masaleiro/HacKeyboard/Pre-compiled/18f4550_usb_hid_keyboard.asm

; compiler: jal 2.4p (compiled Sep  3 2012)

; command line:  ./jalv2 18f4550_usb_hid_keyboard.jal -s ../lib/ -no-variable-reuse
                                list p=18f4550, r=dec
                                errorlevel -306 ; no page boundary warnings
                                errorlevel -302 ; no bank 0 warnings
                                errorlevel -202 ; no 'argument out of range' warnings

                             __config 0x00300000, 0x24
                             __config 0x00300001, 0x0e
                             __config 0x00300002, 0x39
                             __config 0x00300003, 0x1e
                             __config 0x00300004, 0x00
                             __config 0x00300005, 0x85
                             __config 0x00300006, 0xc0
                             __config 0x00300007, 0x00
                             __config 0x00300008, 0x0f
                             __config 0x00300009, 0xc0
                             __config 0x0030000a, 0x0f
                             __config 0x0030000b, 0xe0
                             __config 0x0030000c, 0x0f
                             __config 0x0030000d, 0x40
v_true                         EQU 1
v_false                        EQU 0
v_high                         EQU 1
v_low                          EQU 0
v_input                        EQU 1
v_output                       EQU 0
v__pic_accum                   EQU 0x0000  ; _pic_accum
v_uir                          EQU 0x0f68  ; uir
v_uir_sofif                    EQU 0x0f68  ; uir_sofif-->uir:6
v_uir_stallif                  EQU 0x0f68  ; uir_stallif-->uir:5
v_uir_idleif                   EQU 0x0f68  ; uir_idleif-->uir:4
v_uir_trnif                    EQU 0x0f68  ; uir_trnif-->uir:3
v_uir_uerrif                   EQU 0x0f68  ; uir_uerrif-->uir:1
v_uir_urstif                   EQU 0x0f68  ; uir_urstif-->uir:0
v_uie                          EQU 0x0f69  ; uie
v_ueir                         EQU 0x0f6a  ; ueir
v_ustat                        EQU 0x0f6c  ; ustat
v_ustat_dir                    EQU 0x0f6c  ; ustat_dir-->ustat:2
v_ucon                         EQU 0x0f6d  ; ucon
v_ucon_pktdis                  EQU 0x0f6d  ; ucon_pktdis-->ucon:4
v_ucon_usben                   EQU 0x0f6d  ; ucon_usben-->ucon:3
v_uaddr                        EQU 0x0f6e  ; uaddr
v_ucfg                         EQU 0x0f6f  ; ucfg
v_uep0                         EQU 0x0f70  ; uep0
v_uep1                         EQU 0x0f71  ; uep1
v_uep2                         EQU 0x0f72  ; uep2
v_uep3                         EQU 0x0f73  ; uep3
v_uep4                         EQU 0x0f74  ; uep4
v_uep5                         EQU 0x0f75  ; uep5
v_uep6                         EQU 0x0f76  ; uep6
v_uep7                         EQU 0x0f77  ; uep7
v_uep8                         EQU 0x0f78  ; uep8
v_uep9                         EQU 0x0f79  ; uep9
v_uep10                        EQU 0x0f7a  ; uep10
v_uep11                        EQU 0x0f7b  ; uep11
v_uep12                        EQU 0x0f7c  ; uep12
v_uep13                        EQU 0x0f7d  ; uep13
v_uep14                        EQU 0x0f7e  ; uep14
v_uep15                        EQU 0x0f7f  ; uep15
v_portb                        EQU 0x0f81  ; portb
v_portc                        EQU 0x0f82  ; portc
v_portd                        EQU 0x0f83  ; portd
v_porte                        EQU 0x0f84  ; porte
v_lata                         EQU 0x0f89  ; lata
v_latb                         EQU 0x0f8a  ; latb
v_pin_b1                       EQU 0x0f81  ; pin_b1-->portb:1
v_pin_b0                       EQU 0x0f81  ; pin_b0-->portb:0
v_latc                         EQU 0x0f8b  ; latc
v_pin_c2                       EQU 0x0f82  ; pin_c2-->portc:2
v_pin_c1                       EQU 0x0f82  ; pin_c1-->portc:1
v_pin_c0                       EQU 0x0f82  ; pin_c0-->portc:0
v_latd                         EQU 0x0f8c  ; latd
v_pin_d2                       EQU 0x0f83  ; pin_d2-->portd:2
v_pin_d0                       EQU 0x0f83  ; pin_d0-->portd:0
v_late                         EQU 0x0f8d  ; late
v_pin_e2                       EQU 0x0f84  ; pin_e2-->porte:2
v_pin_e1                       EQU 0x0f84  ; pin_e1-->porte:1
v_trisa                        EQU 0x0f92  ; trisa
v_trisa_trisa5                 EQU 0x0f92  ; trisa_trisa5-->trisa:5
v_trisa_trisa4                 EQU 0x0f92  ; trisa_trisa4-->trisa:4
v_trisa_trisa3                 EQU 0x0f92  ; trisa_trisa3-->trisa:3
v_trisa_trisa2                 EQU 0x0f92  ; trisa_trisa2-->trisa:2
v_trisa_trisa1                 EQU 0x0f92  ; trisa_trisa1-->trisa:1
v_trisa_trisa0                 EQU 0x0f92  ; trisa_trisa0-->trisa:0
v_trisb                        EQU 0x0f93  ; trisb
v_trisb_trisb7                 EQU 0x0f93  ; trisb_trisb7-->trisb:7
v_trisb_trisb6                 EQU 0x0f93  ; trisb_trisb6-->trisb:6
v_trisb_trisb5                 EQU 0x0f93  ; trisb_trisb5-->trisb:5
v_trisb_trisb4                 EQU 0x0f93  ; trisb_trisb4-->trisb:4
v_trisb_trisb3                 EQU 0x0f93  ; trisb_trisb3-->trisb:3
v_trisb_trisb2                 EQU 0x0f93  ; trisb_trisb2-->trisb:2
v_trisb_trisb1                 EQU 0x0f93  ; trisb_trisb1-->trisb:1
v_trisb_trisb0                 EQU 0x0f93  ; trisb_trisb0-->trisb:0
v_trisc                        EQU 0x0f94  ; trisc
v_trisc_trisc2                 EQU 0x0f94  ; trisc_trisc2-->trisc:2
v_trisc_trisc1                 EQU 0x0f94  ; trisc_trisc1-->trisc:1
v_trisc_trisc0                 EQU 0x0f94  ; trisc_trisc0-->trisc:0
v_trisd                        EQU 0x0f95  ; trisd
v_trisd_trisd7                 EQU 0x0f95  ; trisd_trisd7-->trisd:7
v_trisd_trisd6                 EQU 0x0f95  ; trisd_trisd6-->trisd:6
v_trisd_trisd5                 EQU 0x0f95  ; trisd_trisd5-->trisd:5
v_trisd_trisd4                 EQU 0x0f95  ; trisd_trisd4-->trisd:4
v_trisd_trisd2                 EQU 0x0f95  ; trisd_trisd2-->trisd:2
v_trisd_trisd0                 EQU 0x0f95  ; trisd_trisd0-->trisd:0
v_trise                        EQU 0x0f96  ; trise
v_trise_trise2                 EQU 0x0f96  ; trise_trise2-->trise:2
v_trise_trise1                 EQU 0x0f96  ; trise_trise1-->trise:1
v_trise_trise0                 EQU 0x0f96  ; trise_trise0-->trise:0
v_pie2                         EQU 0x0fa0  ; pie2
v_pie2_usbie                   EQU 0x0fa0  ; pie2_usbie-->pie2:5
v_pir2                         EQU 0x0fa1  ; pir2
v_pir2_usbif                   EQU 0x0fa1  ; pir2_usbif-->pir2:5
v_eecon1                       EQU 0x0fa6  ; eecon1
v_eecon1_eepgd                 EQU 0x0fa6  ; eecon1_eepgd-->eecon1:7
v_eecon1_cfgs                  EQU 0x0fa6  ; eecon1_cfgs-->eecon1:6
v_eecon1_wren                  EQU 0x0fa6  ; eecon1_wren-->eecon1:2
v_eecon1_wr                    EQU 0x0fa6  ; eecon1_wr-->eecon1:1
v_eecon1_rd                    EQU 0x0fa6  ; eecon1_rd-->eecon1:0
v_eecon2                       EQU 0x0fa7  ; eecon2
v_eedata                       EQU 0x0fa8  ; eedata
v_eeadr                        EQU 0x0fa9  ; eeadr
v_cmcon                        EQU 0x0fb4  ; cmcon
v_adcon2                       EQU 0x0fc0  ; adcon2
v_adcon1                       EQU 0x0fc1  ; adcon1
v_adcon0                       EQU 0x0fc2  ; adcon0
v__status                      EQU 0x0fd8  ; _status
v__z                           EQU 2
v__c                           EQU 0
v__banked                      EQU 1
v__access                      EQU 0
v_fsr1l                        EQU 0x0fe1  ; fsr1l
v_fsr1h                        EQU 0x0fe2  ; fsr1h
v_postinc1                     EQU 0x0fe6  ; postinc1
v__fsr0l                       EQU 0x0fe9  ; _fsr0l
v__fsr0h                       EQU 0x0fea  ; _fsr0h
v__ind                         EQU 0x0fef  ; _ind
v_intcon                       EQU 0x0ff2  ; intcon
v_intcon_gie                   EQU 0x0ff2  ; intcon_gie-->intcon:7
v__tablat                      EQU 0x0ff5  ; _tablat
v__tblptr                      EQU 0x0ff6  ; _tblptr
v_usb_hid_endpoint             EQU 1
v_usb_in_delivery_buffer_loc   EQU 1144
v_usb_delivery_buffer          EQU 0x0478  ; usb_delivery_buffer
v_usb_delivery_bytes_max_send  EQU 0x0012  ; usb_delivery_bytes_max_send
v_usb_delivery_bytes_sent      EQU 0x0013  ; usb_delivery_bytes_sent
v_usb_delivery_buffer_size     EQU 0x0014  ; usb_delivery_buffer_size
v_usb_delivery_bytes_to_send   EQU 0x0015  ; usb_delivery_bytes_to_send
v_usb_sdp                      EQU 0x04f8  ; usb_sdp
v_usb_sdp_request_type         EQU 0x04f8  ; usb_sdp_request_type
v_usb_sdp_request              EQU 0x04f9  ; usb_sdp_request
v_usb_sdp_value                EQU 0x04fa  ; usb_sdp_value
v_usb_sdp_length               EQU 0x04fe  ; usb_sdp_length
v_usb_status_idle              EQU 0
v_usb_status_set_address       EQU 1
v_usb_state_powered            EQU 0
v_usb_state_default            EQU 1
v_usb_state_address            EQU 2
v_usb_state_configured         EQU 3
v_usb_cm_idle                  EQU 0
v_usb_cm_ctrl_write_data_stage_class EQU 2
v_usb_cm_ctrl_read_data_stage  EQU 3
v_usb_cm_ctrl_read_data_stage_class EQU 4
v_usb_cm_ctrl_read_awaiting_status EQU 5
v_usb_cm_ctrl_write_sending_status EQU 6
v_usb_request_set_address      EQU 5
v_usb_request_get_descriptor   EQU 6
v_usb_request_set_configuration EQU 9
v_usb_request_get_interface    EQU 10
v_usb_pid_out                  EQU 1
v_usb_pid_in                   EQU 9
v_usb_pid_setup                EQU 13
v_usb_pid_ack                  EQU 2
v_usb_state                    EQU 0x0016  ; usb_state
v_usb_status                   EQU 0x0017  ; usb_status
v_usb_control_mode             EQU 0x0018  ; usb_control_mode
v_usb_address                  EQU 0x0019  ; usb_address
v_usb_bd_array                 EQU 0x0400  ; usb_bd_array
v_usb_bd0out                   EQU 0x0400  ; usb_bd0out
v_usb_bd0out_stat              EQU 0x0400  ; usb_bd0out_stat-->usb_bd0out
v_usb_bd0out_cnt               EQU 0x0401  ; usb_bd0out_cnt-->usb_bd0out+1
v_usb_bd0out_addr              EQU 0x0402  ; usb_bd0out_addr-->usb_bd0out+2
v_usb_bd0in                    EQU 0x0404  ; usb_bd0in
v_usb_bd0in_stat               EQU 0x0404  ; usb_bd0in_stat-->usb_bd0in
v_usb_bd0in_cnt                EQU 0x0405  ; usb_bd0in_cnt-->usb_bd0in+1
v_usb_bd0in_addr               EQU 0x0406  ; usb_bd0in_addr-->usb_bd0in+2
v_usb_bd1out                   EQU 0x0408  ; usb_bd1out
v_usb_bd1out_stat              EQU 0x0408  ; usb_bd1out_stat-->usb_bd1out
v_usb_bd1out_cnt               EQU 0x0409  ; usb_bd1out_cnt-->usb_bd1out+1
v_usb_bd1out_addr              EQU 0x040a  ; usb_bd1out_addr-->usb_bd1out+2
v_usb_bd1in                    EQU 0x040c  ; usb_bd1in
v_usb_bd1in_stat               EQU 0x040c  ; usb_bd1in_stat-->usb_bd1in
v_usb_bd1in_cnt                EQU 0x040d  ; usb_bd1in_cnt-->usb_bd1in+1
v_usb_bd1in_addr               EQU 0x040e  ; usb_bd1in_addr-->usb_bd1in+2
v_ep1inen                      EQU 0x0f71  ; ep1inen-->uep1:1
v_ep1outen                     EQU 0x0f71  ; ep1outen-->uep1:2
v_ep1condis                    EQU 0x0f71  ; ep1condis-->uep1:3
v_ep1hshk                      EQU 0x0f71  ; ep1hshk-->uep1:4
v_usb_dt_device                EQU 1
v_usb_dt_configuration         EQU 2
v_usb_dt_string                EQU 3
v_usb_dt_hid_report            EQU 34
v_usb_ep0_out_size             EQU 8
v_usb_ep0_out_addr             EQU 1040
v_usb_ep0_in_size              EQU 8
v_usb_ep0_in_addr              EQU 1048
v_usb_ep1_out_size             EQU 8
v_usb_ep1_out_addr             EQU 1056
v_usb_ep1_in_addr              EQU 1064
v_usb_keyboard_mkey_left_ctrl  EQU 1
v_usb_keyboard_mkey_left_shift EQU 2
v_usb_keyboard_mkey_left_alt   EQU 4
v_usb_keyboard_mkey_left_gui   EQU 8
v_usb_keyboard_mkey_right_ctrl EQU 16
v_usb_keyboard_mkey_right_shift EQU 32
v_usb_keyboard_mkey_right_alt  EQU 64
v_usb_keyboard_mkey_right_gui  EQU 128
v__usb_hid_can_tx              EQU 0x01b0  ; _usb_hid_can_tx-->_bitbucket:0
v_usb_hcr_get_report           EQU 1
v_usb_hcr_get_idle             EQU 2
v_usb_hcr_get_protocol         EQU 3
v_usb_hcr_set_report           EQU 9
v_usb_hcr_set_idle             EQU 10
v_usb_hcr_set_protocol         EQU 11
v_pos                          EQU 0x001a  ; pos
v_inccolor                     EQU 0x001b  ; inccolor
v_deccolor                     EQU 0x001c  ; deccolor
v_colorfactorr                 EQU 0x001d  ; colorfactorr
v_colorfactorg                 EQU 0x001e  ; colorfactorg
v_colorfactorb                 EQU 0x001f  ; colorfactorb
v_direction                    EQU 0x0020  ; direction
v_rgbcolour                    EQU 0x0021  ; rgbcolour
v_ledmode                      EQU 0x0024  ; ledmode
v_timecounter                  EQU 0x0025  ; timecounter
v_aux                          EQU 0x0027  ; aux
v_aux2                         EQU 0x0028  ; aux2
v_f_index                      EQU 0x0029  ; f_index
v___modifier_1                 EQU 0x0035  ; modifier
v_mode                         EQU 0x0036  ; mode
v_color_mode                   EQU 0x0037  ; color_mode
v_log_mode                     EQU 0x0038  ; log_mode
v_save_mode                    EQU 0x0039  ; save_mode
v_counter                      EQU 0x003a  ; counter
v_ssa                          EQU 0x0052  ; ssa
v_logcounter                   EQU 0x006a  ; logcounter
v_csa                          EQU 0x006e  ; csa
v_cpa                          EQU 0x0070  ; cpa
v_cla                          EQU 0x0072  ; cla
v_inhibit                      EQU 0x0074  ; inhibit
v_g                            EQU 0x0075  ; g
v_d                            EQU 0x0076  ; d
v_z                            EQU 0x0077  ; z
v___r_1                        EQU 0x0078  ; r
v_key_index                    EQU 0x0079  ; key_index
v___hid_report_in_3            EQU 0x007a  ; hid_report_in
v_queue                        EQU 0x0082  ; queue
v_key_pressed                  EQU 0x0089  ; key_pressed
v_current                      EQU 0x0100  ; current
v_previous                     EQU 0x0158  ; previous
v_bounce                       EQU 0x0200  ; bounce
v_type                         EQU 0x0258  ; type
v_keys                         EQU 0x0300  ; keys
v_red                          EQU 0x00e1  ; red
v_green                        EQU 0x00e5  ; green
v_blue                         EQU 0x00e9  ; blue
v____temp_54                   EQU 0x00ed  ; _temp
v_red_                         EQU 0x00f1  ; red_
v_green_                       EQU 0x00f2  ; green_
v_blue_                        EQU 0x00f3  ; blue_
v_i                            EQU 0x00f4  ; i
v__floop42                     EQU 0x00f5  ; _floop42
v__floop43                     EQU 0x00f6  ; _floop43
v__floop44                     EQU 0x00f7  ; _floop44
v__bitbucket                   EQU 0x01b0  ; _bitbucket
v__pic_temp                    EQU 0x0008  ; _pic_temp-->_pic_state
v__pic_pointer                 EQU 0x000e  ; _pic_pointer
v__pic_state                   EQU 0x0008  ; _pic_state
v___x_122                      EQU 0x0f8d  ; x-->late
v___offset_22                  EQU 0x00f8  ; offset
v___data_27                    EQU 0x00fa  ; data
v___offset_23                  EQU 0x00fb  ; offset
v___data_28                    EQU 0x00fd  ; data
v___offset_24                  EQU 0x00fe  ; offset
v___data_29                    EQU 0x01d0  ; data
v___offset_25                  EQU 0x01d1  ; offset
v___data_30                    EQU 0x01d3  ; data
v___offset_26                  EQU 0x01d4  ; offset
v___data_31                    EQU 0x01d6  ; data
v___offset_27                  EQU 0x01d7  ; offset
v___data_32                    EQU 0x01d9  ; data
v___offset_28                  EQU 0x01da  ; offset
v___data_33                    EQU 0x01dc  ; data
v___offset_29                  EQU 0x01dd  ; offset
v___data_34                    EQU 0x01df  ; data
v___offset_30                  EQU 0x01e0  ; offset
v___data_35                    EQU 0x01e2  ; data
v___offset_31                  EQU 0x01e3  ; offset
v___data_36                    EQU 0x01e5  ; data
v___offset_32                  EQU 0x01e6  ; offset
v___data_37                    EQU 0x01e8  ; data
v___offset_33                  EQU 0x01e9  ; offset
v___data_38                    EQU 0x01eb  ; data
v___offset_34                  EQU 0x01ec  ; offset
v___data_39                    EQU 0x01ee  ; data
v___offset_35                  EQU 0x01ef  ; offset
v___data_40                    EQU 0x01f1  ; data
v___offset_36                  EQU 0x01f3  ; offset
v___data_41                    EQU 0x01f5  ; data
v___offset_37                  EQU 0x01f7  ; offset
v___data_42                    EQU 0x01f9  ; data
v___offset_38                  EQU 0x01fb  ; offset
v___data_43                    EQU 0x01fd  ; data
v___offset_39                  EQU 0x02b0  ; offset
v___data_44                    EQU 0x02b2  ; data
v___offset_40                  EQU 0x02b4  ; offset
v___data_45                    EQU 0x02b6  ; data
v___offset_41                  EQU 0x02b8  ; offset
v___data_46                    EQU 0x02ba  ; data
v___offset_42                  EQU 0x02bc  ; offset
v___data_47                    EQU 0x02be  ; data
v___offset_43                  EQU 0x02c0  ; offset
v___data_48                    EQU 0x02c2  ; data
v___offset_44                  EQU 0x02c4  ; offset
v___data_49                    EQU 0x02c6  ; data
v___offset_45                  EQU 0x02c8  ; offset
v___data_50                    EQU 0x02ca  ; data
v___offset_46                  EQU 0x02cc  ; offset
v___data_51                    EQU 0x02ce  ; data
v___offset_47                  EQU 0x02d0  ; offset
v___data_52                    EQU 0x02d2  ; data
v___data_53                    EQU 0x02d6  ; data
v___tempword_3                 EQU 0x02d6  ; tempword-->data53
v____temp_55                   EQU 0x02da  ; _temp
v___x_147                      EQU 0x0f8c  ; x-->latd:2
v__btemp127                    EQU 0x01b0  ; _btemp127-->_bitbucket:4
v__floop45                     EQU 0x01ff  ; _floop45
v__btemp330                    EQU 0x01b0  ; _btemp330-->_bitbucket:207
v__btemp331                    EQU 0x01b0  ; _btemp331-->_bitbucket:208
v__btemp332                    EQU 0x01b0  ; _btemp332-->_bitbucket:209
v__btemp333                    EQU 0x01b0  ; _btemp333-->_bitbucket:210
v__btemp334                    EQU 0x01b0  ; _btemp334-->_bitbucket:211
v__btemp335                    EQU 0x01b0  ; _btemp335-->_bitbucket:212
v__btemp336                    EQU 0x01b0  ; _btemp336-->_bitbucket:213
v__btemp337                    EQU 0x01b0  ; _btemp337-->_bitbucket:214
v__btemp338                    EQU 0x01b0  ; _btemp338-->_bitbucket:215
v___x_148                      EQU 0x0f8c  ; x-->latd:4
v___x_149                      EQU 0x0f8c  ; x-->latd:4
v___x_150                      EQU 0x0f8c  ; x-->latd:5
v___x_151                      EQU 0x0f8c  ; x-->latd:5
v___x_152                      EQU 0x0f8c  ; x-->latd:6
v___x_153                      EQU 0x0f8c  ; x-->latd:6
v___x_154                      EQU 0x0f8c  ; x-->latd:7
v___x_155                      EQU 0x0f8c  ; x-->latd:7
v___x_156                      EQU 0x0f8a  ; x-->latb:2
v___x_157                      EQU 0x0f8a  ; x-->latb:2
v___x_158                      EQU 0x0f8a  ; x-->latb:3
v___x_159                      EQU 0x0f8a  ; x-->latb:3
v___x_160                      EQU 0x0f8a  ; x-->latb:4
v___x_161                      EQU 0x0f8a  ; x-->latb:4
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
v__btemp267                    EQU 0x01b0  ; _btemp267-->_bitbucket:144
v__btemp268                    EQU 0x01b0  ; _btemp268-->_bitbucket:145
v__btemp269                    EQU 0x01b0  ; _btemp269-->_bitbucket:146
v__btemp277                    EQU 0x01b0  ; _btemp277-->_bitbucket:154
v__btemp278                    EQU 0x01b0  ; _btemp278-->_bitbucket:155
v__btemp279                    EQU 0x01b0  ; _btemp279-->_bitbucket:156
v__btemp287                    EQU 0x01b0  ; _btemp287-->_bitbucket:164
v__btemp288                    EQU 0x01b0  ; _btemp288-->_bitbucket:165
v__btemp289                    EQU 0x01b0  ; _btemp289-->_bitbucket:166
v___x_182                      EQU 0x0f8c  ; x-->latd:2
v___x_183                      EQU 0x0f8c  ; x-->latd:2
v__btemp292                    EQU 0x01b0  ; _btemp292-->_bitbucket:169
v__btemp293                    EQU 0x01b0  ; _btemp293-->_bitbucket:170
v__btemp294                    EQU 0x01b0  ; _btemp294-->_bitbucket:171
v__btemp296                    EQU 0x01b0  ; _btemp296-->_bitbucket:173
v__btemp297                    EQU 0x01b0  ; _btemp297-->_bitbucket:174
v__btemp298                    EQU 0x01b0  ; _btemp298-->_bitbucket:175
v__btemp300                    EQU 0x01b0  ; _btemp300-->_bitbucket:177
v__btemp301                    EQU 0x01b0  ; _btemp301-->_bitbucket:178
v__btemp302                    EQU 0x01b0  ; _btemp302-->_bitbucket:179
v__btemp304                    EQU 0x01b0  ; _btemp304-->_bitbucket:181
v__btemp305                    EQU 0x01b0  ; _btemp305-->_bitbucket:182
v__btemp306                    EQU 0x01b0  ; _btemp306-->_bitbucket:183
v__btemp308                    EQU 0x01b0  ; _btemp308-->_bitbucket:185
v__btemp309                    EQU 0x01b0  ; _btemp309-->_bitbucket:186
v__btemp310                    EQU 0x01b0  ; _btemp310-->_bitbucket:187
v__btemp319                    EQU 0x01b0  ; _btemp319-->_bitbucket:196
v__btemp320                    EQU 0x01b0  ; _btemp320-->_bitbucket:197
v__btemp321                    EQU 0x01b0  ; _btemp321-->_bitbucket:198
v___offset_50                  EQU 0x02ed  ; offset
v___data_60                    EQU 0x02ef  ; data
v___tempword_6                 EQU 0x02ef  ; tempword-->data60
v____temp_67                   EQU 0x02f3  ; _temp
v__btemp352                    EQU 0x01b0  ; _btemp352-->_bitbucket:229
v__btemp353                    EQU 0x01b0  ; _btemp353-->_bitbucket:230
v__btemp354                    EQU 0x01b0  ; _btemp354-->_bitbucket:231
v__btemp355                    EQU 0x01b0  ; _btemp355-->_bitbucket:232
v__btemp356                    EQU 0x01b0  ; _btemp356-->_bitbucket:233
v__btemp360                    EQU 0x01b0  ; _btemp360-->_bitbucket:237
v__btemp361                    EQU 0x01b0  ; _btemp361-->_bitbucket:238
v__btemp362                    EQU 0x01b0  ; _btemp362-->_bitbucket:239
v__btemp363                    EQU 0x01b0  ; _btemp363-->_bitbucket:240
v__btemp364                    EQU 0x01b0  ; _btemp364-->_bitbucket:241
v__floop46                     EQU 0x02f5  ; _floop46
v___rr_3                       EQU 0x02f6  ; set_color:rr
v___gg_3                       EQU 0x02f7  ; set_color:gg
v___bb_3                       EQU 0x02f8  ; set_color:bb
v___a_5                        EQU 0x02f9  ; set_color:a
v___b_5                        EQU 0x02fa  ; set_color:b
v__floop29                     EQU 0x02fb  ; set_color:_floop29
v__floop30                     EQU 0x02fc  ; set_color:_floop30
v__floop34                     EQU 0x02fd  ; set_color:_floop34
v__floop38                     EQU 0x02fe  ; set_color:_floop38
v__floop31                     EQU 0x02ff  ; set_color:_floop31
v__floop32                     EQU 0x0358  ; set_color:_floop32
v___x_135                      EQU 0x0f8a  ; set_color:x-->latb:0
v___x_136                      EQU 0x0f8a  ; set_color:x-->latb:0
v__floop33                     EQU 0x0359  ; set_color:_floop33
v___x_137                      EQU 0x0f8a  ; set_color:x-->latb:0
v___x_138                      EQU 0x0f8a  ; set_color:x-->latb:0
v__floop35                     EQU 0x035a  ; set_color:_floop35
v__floop36                     EQU 0x035b  ; set_color:_floop36
v___x_139                      EQU 0x0f8a  ; set_color:x-->latb:0
v___x_140                      EQU 0x0f8a  ; set_color:x-->latb:0
v__floop37                     EQU 0x035c  ; set_color:_floop37
v___x_141                      EQU 0x0f8a  ; set_color:x-->latb:0
v___x_142                      EQU 0x0f8a  ; set_color:x-->latb:0
v__floop39                     EQU 0x035d  ; set_color:_floop39
v__floop40                     EQU 0x035e  ; set_color:_floop40
v___x_143                      EQU 0x0f8a  ; set_color:x-->latb:0
v___x_144                      EQU 0x0f8a  ; set_color:x-->latb:0
v__floop41                     EQU 0x035f  ; set_color:_floop41
v___x_145                      EQU 0x0f8a  ; set_color:x-->latb:0
v___x_146                      EQU 0x0f8a  ; set_color:x-->latb:0
v___rr_1                       EQU 0x0360  ; set_color_single_led:rr
v___gg_1                       EQU 0x0361  ; set_color_single_led:gg
v___bb_1                       EQU 0x0362  ; set_color_single_led:bb
v___a_4                        EQU 0x0363  ; set_color_single_led:a
v___b_4                        EQU 0x0364  ; set_color_single_led:b
v__floop17                     EQU 0x0365  ; set_color_single_led:_floop17
v__floop21                     EQU 0x0366  ; set_color_single_led:_floop21
v__floop25                     EQU 0x0367  ; set_color_single_led:_floop25
v__floop18                     EQU 0x0368  ; set_color_single_led:_floop18
v__floop19                     EQU 0x0369  ; set_color_single_led:_floop19
v___x_123                      EQU 0x0f8a  ; set_color_single_led:x-->latb:0
v___x_124                      EQU 0x0f8a  ; set_color_single_led:x-->latb:0
v__floop20                     EQU 0x036a  ; set_color_single_led:_floop20
v___x_125                      EQU 0x0f8a  ; set_color_single_led:x-->latb:0
v___x_126                      EQU 0x0f8a  ; set_color_single_led:x-->latb:0
v__floop22                     EQU 0x036b  ; set_color_single_led:_floop22
v__floop23                     EQU 0x036c  ; set_color_single_led:_floop23
v___x_127                      EQU 0x0f8a  ; set_color_single_led:x-->latb:0
v___x_128                      EQU 0x0f8a  ; set_color_single_led:x-->latb:0
v__floop24                     EQU 0x036d  ; set_color_single_led:_floop24
v___x_129                      EQU 0x0f8a  ; set_color_single_led:x-->latb:0
v___x_130                      EQU 0x0f8a  ; set_color_single_led:x-->latb:0
v__floop26                     EQU 0x036e  ; set_color_single_led:_floop26
v__floop27                     EQU 0x036f  ; set_color_single_led:_floop27
v___x_131                      EQU 0x0f8a  ; set_color_single_led:x-->latb:0
v___x_132                      EQU 0x0f8a  ; set_color_single_led:x-->latb:0
v__floop28                     EQU 0x0370  ; set_color_single_led:_floop28
v___x_133                      EQU 0x0f8a  ; set_color_single_led:x-->latb:0
v___x_134                      EQU 0x0f8a  ; set_color_single_led:x-->latb:0
v___a_3                        EQU 0x0371  ; playlog:a
v___b_3                        EQU 0x0372  ; playlog:b
v___c_1                        EQU 0x0373  ; playlog:c
v___position_1                 EQU 0x0374  ; play:position
v___a_2                        EQU 0x0375  ; play:a
v___b_2                        EQU 0x0376  ; play:b
v_c                            EQU 0x0377  ; play:c
v____temp_61                   EQU 0x0378  ; play:_temp
v___mod_3                      EQU 0x0379  ; log:mod
v___data_57                    EQU 0x037a  ; log:data
v___mod_1                      EQU 0x037b  ; save_data_ext_eeprom:mod
v___data_55                    EQU 0x037c  ; save_data_ext_eeprom:data
v_a                            EQU 0x037d  ; save_data_ext_eeprom:a
v____temp_59                   EQU 0x037e  ; save_data_ext_eeprom:_temp
v___key_ind_3                  EQU 0x0380  ; key_press_:key_ind
v___y_1                        EQU 0x0381  ; key_press_:y
v____temp_58                   EQU 0x0382  ; key_press_:_temp
v__floop16                     EQU 0x0383  ; key_press_:_floop16
v___key_ind_1                  EQU 0x0384  ; key_release_:key_ind
v____temp_57                   EQU 0x0385  ; key_release_:_temp
v__floop15                     EQU 0x0386  ; key_release_:_floop15
v_y                            EQU 0x0387  ; send:y
v__floop14                     EQU 0x0388  ; send:_floop14
v____temp_56                   EQU 0x0389  ; send:_temp
v___modifier_key_1             EQU 0x038a  ; ush_keyboard_send_key:modifier_key
v___key_1                      EQU 0x038b  ; ush_keyboard_send_key:key
v___hid_report_in_2            EQU 0x038c  ; ush_keyboard_send_key:hid_report_in
v__hid_report_in_count         EQU 0x0394  ; _usb_hid_tx_report:_hid_report_in_count
v___hid_report_in_1            EQU 0x0396  ; _usb_hid_tx_report:hid_report_in
v___cnt_1                      EQU 0x0399  ; _usb_hid_tx_report:cnt
v__floop13                     EQU 0x039a  ; usb_handle_isr:_floop13
v___end_point_4                EQU 0x039b  ; _usb_handle_transaction:end_point
v_pid                          EQU 0x039c  ; _usb_handle_transaction:pid
v____temp_52                   EQU 0x039d  ; _usb_handle_transaction:_temp
v_src                          EQU 0x0410  ; _usb_handle_transaction:src
v___idx_2                      EQU 0x039e  ; _usb_handle_transaction:idx
v___idx_3                      EQU 0x039f  ; _usb_handle_transaction:idx
v_addr                         EQU 0x03a0  ; _usb_handle_transaction:addr
v_bt_addr                      EQU 0x03a0  ; _usb_handle_transaction:bt_addr-->addr
v_request                      EQU 0x0011  ; _usb_handle_standard_request:request
v_wbt_value                    EQU 0x04fa  ; _usb_handle_standard_request:wbt_value-->usb_sdp_value
v_wbt_length                   EQU 0x04fe  ; _usb_handle_standard_request:wbt_length-->usb_sdp_length
v_descriptor_type              EQU 0x03a2  ; _usb_handle_standard_request:descriptor_type
v_descriptor_num               EQU 0x03a3  ; _usb_handle_standard_request:descriptor_num
v___dts_bit_5                  EQU 0x0404  ; _usb_handle_standard_request:dts_bit-->usb_bd0in_stat:6
v___req01_1                    EQU 0x03a4  ; usb_handle_class_ctrl_write_callback:req01
v_req01                        EQU 0x03a5  ; usb_handle_class_request_callback:req01
v_len                          EQU 0x03a6  ; usb_handle_class_request_callback:len
v___end_point_1                EQU 0x03a8  ; usb_prime_epx_out:end_point
v___size_1                     EQU 0x03a9  ; usb_prime_epx_out:size
v____temp_51                   EQU 0x03aa  ; usb_prime_epx_out:_temp
v___idx_1                      EQU 0x03ab  ; usb_prime_epx_out:idx
v_new_value                    EQU 0x03ac  ; usb_prime_ep0_out:new_value
v___endpoint_1                 EQU 0x03ad  ; usb_send_data:endpoint
v____data_count_1              EQU 0x03ae  ; usb_send_data:_data_count
v___data_26                    EQU 0x03b0  ; usb_send_data:data
v___byte_cnt_2                 EQU 0x03b3  ; usb_send_data:byte_cnt
v___is_new_sequence_1          EQU 0x03b4  ; usb_send_data:is_new_sequence-->_bitbucket37:0
v____bitbucket_37              EQU 0x03b4  ; usb_send_data:_bitbucket
v___dts_bit_3                  EQU 0x0404  ; usb_send_data:dts_bit-->usb_bd0in_stat:6
v___dts_bit_4                  EQU 0x040c  ; usb_send_data:dts_bit-->usb_bd1in_stat:6
v___data_24                    EQU 0x03b5  ; usb_send_one_byte:data
v___dts_bit_2                  EQU 0x0404  ; usb_send_one_byte:dts_bit-->usb_bd0in_stat:6
v___dts_bit_1                  EQU 0x0404  ; usb_send_empty_data_pkt:dts_bit-->usb_bd0in_stat:6
v_own_bit                      EQU 0x0404  ; usb_send_data_chunk:own_bit-->usb_bd0in_stat:7
v_byte_cnt                     EQU 0x03b6  ; usb_send_data_chunk:byte_cnt
v_dts_bit                      EQU 0x0404  ; usb_send_data_chunk:dts_bit-->usb_bd0in_stat:6
v___dst_1                      EQU 0x03b7  ; _usb_copy_array_to_ram:dst
v___data_22                    EQU 0x03b9  ; _usb_copy_array_to_ram:data
v___num_bytes_1                EQU 0x03bc  ; _usb_copy_array_to_ram:num_bytes
v_index                        EQU 0x03bd  ; _usb_copy_array_to_ram:index
v_dst_ptr                      EQU 0x03b7  ; _usb_copy_array_to_ram:dst_ptr-->dst1
v__floop12                     EQU 0x03be  ; _usb_copy_array_to_ram:_floop12
v___ic_address_3               EQU 0x03bf  ; ee_24lc256_write:ic_address
v___mem_address_3              EQU 0x03c0  ; ee_24lc256_write:mem_address
v___data_19                    EQU 0x03c2  ; ee_24lc256_write:data
v___address_low_1              EQU 0x03c3  ; ee_24lc256_write:address_low
v___address_high_1             EQU 0x03c4  ; ee_24lc256_write:address_high
v___address_bytes_1            EQU 0x03c0  ; ee_24lc256_write:address_bytes-->mem_address3
v___ic_address_1               EQU 0x03c5  ; ee_24lc256_read:ic_address
v___mem_address_1              EQU 0x03c6  ; ee_24lc256_read:mem_address
v___data_17                    EQU 0x03c8  ; ee_24lc256_read:data
v_address_low                  EQU 0x03c9  ; ee_24lc256_read:address_low
v_address_high                 EQU 0x03ca  ; ee_24lc256_read:address_high
v_address_bytes                EQU 0x03c6  ; ee_24lc256_read:address_bytes-->mem_address1
v____temp_48                   EQU 0x03cb  ; ee_24lc256_read:_temp
v___ack_1                      EQU 0x03ce  ; i2c_receive_byte:ack-->_bitbucket45:0
v_ret                          EQU 0x03cc  ; i2c_receive_byte:ret
v___b_1                        EQU 0x03cc  ; i2c_receive_byte:b-->ret:0
v__floop11                     EQU 0x03cd  ; i2c_receive_byte:_floop11
v____bitbucket_45              EQU 0x03ce  ; i2c_receive_byte:_bitbucket
v___x_117                      EQU 0x03cf  ; i2c_transmit_byte:x
v_b                            EQU 0x03cf  ; i2c_transmit_byte:b-->x117:7
v_r                            EQU 0x03d1  ; i2c_transmit_byte:r-->_bitbucket46:0
v__floop10                     EQU 0x03d0  ; i2c_transmit_byte:_floop10
v____bitbucket_46              EQU 0x03d1  ; i2c_transmit_byte:_bitbucket
v__floop9                      EQU 0x03d2  ; i2c_initialize:_floop9
v___x_114                      EQU 0x0f8a  ; i2c_initialize:x-->latb:1
v___x_115                      EQU 0x0f8a  ; i2c_initialize:x-->latb:0
v___x_119                      EQU 0x03d3  ; _i2c_bit_out:x-->_bitbucket51:0
v____bitbucket_51              EQU 0x03d3  ; _i2c_bit_out:_bitbucket
v___x_121                      EQU 0x03d4  ; _i2c_bit_in:x-->_bitbucket52:0
v____bitbucket_52              EQU 0x03d4  ; _i2c_bit_in:_bitbucket
v___data_15                    EQU 0       ; data_eeprom_write_dword(): data
v___data_11                    EQU 0       ; data_eeprom_read_dword(): data
v___offset_15                  EQU 0x03d5  ; data_eeprom_write_word:offset
v___data_9                     EQU 0x03d7  ; data_eeprom_write_word:data
v___tempbyte_1                 EQU 0x03d7  ; data_eeprom_write_word:tempbyte-->data9
v____temp_42                   EQU 0x03d9  ; data_eeprom_write_word:_temp
v___offset_11                  EQU 0x03db  ; data_eeprom_read_word:offset
v___data_6                     EQU 0x03dd  ; data_eeprom_read_word:data
v_tempbyte                     EQU 0x03dd  ; data_eeprom_read_word:tempbyte-->data6
v____temp_41                   EQU 0x03df  ; data_eeprom_read_word:_temp
v___offset_6                   EQU 0x03e1  ; data_eeprom_write:offset
v___data_3                     EQU 0x03e3  ; data_eeprom_write:data
v_gie_old                      EQU 0x03e4  ; data_eeprom_write:gie_old-->_bitbucket61:0
v____bitbucket_61              EQU 0x03e4  ; data_eeprom_write:_bitbucket
v___offset_7                   EQU 0x03e5  ; data_eeprom_write:offset
v___tempoffset_2               EQU 0x03e5  ; data_eeprom_write:tempoffset-->offset7
v___offset_3                   EQU 0x03e7  ; data_eeprom_read:offset
v___data_1                     EQU 0x03e9  ; data_eeprom_read:data
v___offset_4                   EQU 0x03ea  ; data_eeprom_read:offset
v___tempoffset_1               EQU 0x03ea  ; data_eeprom_read:tempoffset-->offset4
v___offset_1                   EQU 0       ; _prepare_eeprom_access(): offset
v___n_3                        EQU 0x03ec  ; delay_1ms:n
v__floop3                      EQU 0x03ee  ; delay_1ms:_floop3
v__floop4                      EQU 0x03f0  ; delay_1ms:_floop4
;   35 include 18f4550
                               org      0
                               goto     l__main
l__data_usb_device_descriptor
                               db       0x12,0x01,0x00,0x02,0x00,0x00,0x00,0x08
                               db       0xd8,0x04,0x55,0x00,0x01,0x00,0x01,0x02
                               db       0x00,0x01
l__data_usb_hid_report1
                               db       0x05,0x01,0x09,0x06,0xa1,0x01,0x05,0x07
                               db       0x19,0xe0,0x29,0xe7,0x15,0x00,0x25,0x01
                               db       0x75,0x01,0x95,0x08,0x81,0x02,0x95,0x01
                               db       0x75,0x08,0x81,0x03,0x95,0x05,0x75,0x01
                               db       0x05,0x08,0x19,0x01,0x29,0x05,0x91,0x02
                               db       0x95,0x01,0x75,0x03,0x91,0x03,0x95,0x06
                               db       0x75,0x08,0x15,0x00,0x25,0x65,0x05,0x07
                               db       0x19,0x00,0x29,0x65,0x81,0x00,0xc0,0x00
l__data_usb_configuration_descriptor
                               db       0x09,0x02,0x22,0x00,0x01,0x01,0x00,0x80
                               db       0x64,0x09,0x04,0x00,0x00,0x01,0x03,0x01
                               db       0x01,0x00,0x09,0x21,0x11,0x01,0x00,0x01
                               db       0x22,0x3f,0x00,0x07,0x05,0x81,0x03,0x08
                               db       0x00,0x01
l__data_usb_string0
                               db       0x04,0x03,0x09,0x04
l__data_usb_string1
                               db       0x36,0x03,0x4d,0x00,0x69,0x00,0x63,0x00
                               db       0x72,0x00,0x6f,0x00,0x63,0x00,0x68,0x00
                               db       0x69,0x00,0x70,0x00,0x20,0x00,0x54,0x00
                               db       0x65,0x00,0x63,0x00,0x68,0x00,0x6e,0x00
                               db       0x6f,0x00,0x6c,0x00,0x6f,0x00,0x67,0x00
                               db       0x79,0x00,0x2c,0x00,0x20,0x00,0x49,0x00
                               db       0x6e,0x00,0x63,0x00,0x2e,0x00
l__data_usb_string2
                               db       0x2a,0x03,0x4a,0x00,0x41,0x00,0x4c,0x00
                               db       0x20,0x00,0x48,0x00,0x49,0x00,0x44,0x00
                               db       0x20,0x00,0x4b,0x00,0x65,0x00,0x62,0x00
                               db       0x6f,0x00,0x61,0x00,0x72,0x00,0x64,0x00
                               db       0x20,0x00,0x44,0x00,0x65,0x00,0x6d,0x00
                               db       0x6f,0x00
l__pic_pointer_read
                               btfsc    v__pic_pointer+2, 7,v__banked
                               goto     l__l1563
                               btfsc    v__pic_pointer+2, 6,v__banked
                               goto     l__l1564
                               movf     v__pic_pointer+1,w,v__banked
                               movwf    v__fsr0h,v__access
                               movf     v__pic_pointer,w,v__banked
                               movwf    v__fsr0l,v__access
                               movf     v__ind,w,v__access
                               return   
l__l1564
                               movf     v__pic_pointer,w,v__banked
                               movwf    v__tblptr,v__access
                               movf     v__pic_pointer+1,w,v__banked
                               movwf    v__tblptr+1,v__access
                               movf     v__pic_pointer+2,w,v__banked
                               andlw    63
                               movwf    v__tblptr+2,v__access
                               tblrd    *
                               movf     v__tablat,w,v__access
                               return   
l__l1563
                               return   
l__main
; ../lib/18f4550.jal
;  331 procedure PORTA'put(byte in x at LATA) is
                               goto     l__l269
; ../lib/delay.jal
;  113 procedure delay_1ms(word in n) is
l_delay_1ms
;  115    for n loop
                               movf     v___n_3,w,v__banked
                               movwf    v__floop3,v__banked
                               movf     v___n_3+1,w,v__banked
                               movwf    v__floop3+1,v__banked
                               clrf     v__floop4,v__banked
                               clrf     v__floop4+1,v__banked
                               goto     l__l196
l__l195
;  117          _usec_delay(_one_ms_delay)
                               movlb    0
                               movlw    255
                               movwf    v__pic_temp,v__banked
l__l1565
                               movlw    14
                               movwf    v__pic_temp+1,v__banked
l__l1566
                               decfsz   v__pic_temp+1,f,v__banked
                               goto     l__l1566
                               decfsz   v__pic_temp,f,v__banked
                               goto     l__l1565
;  121    end loop
                               movlb    3
                               incf     v__floop4,f,v__banked
                               btfsc    v__status, v__z,v__access
                               incf     v__floop4+1,f,v__banked
l__l196
                               movf     v__floop4,w,v__banked
                               subwf    v__floop3,w,v__banked
                               movlb    0
                               movwf    v__pic_temp,v__banked
                               movlb    3
                               movf     v__floop4+1,w,v__banked
                               subwf    v__floop3+1,w,v__banked
                               movlb    0
                               iorwf    v__pic_temp,w,v__banked
                               btfss    v__status, v__z,v__access
                               goto     l__l195
;  122 end procedure
                               return   
; ../lib/pic_data_eeprom.jal
;   97 procedure  data_eeprom_read(word in offset, byte out data) is
l_data_eeprom_read
;   99    _prepare_eeprom_access(offset)               -- make ready for read
                               movf     v___offset_3,w,v__banked
                               movwf    v___offset_4,v__banked
                               movf     v___offset_3+1,w,v__banked
                               movwf    v___offset_4+1,v__banked
l__l224
                               btfsc    v_eecon1, 1,v__access ; eecon1_wr
                               goto     l__l224
l__l225
                               movf     v___tempoffset_1,w,v__banked
                               movwf    v_eeadr,v__access
                               bcf      v_eecon1, 6,v__access ; eecon1_cfgs
                               bcf      v_eecon1, 7,v__access ; eecon1_eepgd
                               bsf      v_eecon1, 0,v__access ; eecon1_rd
                               movf     v_eedata,w,v__access
                               movwf    v___data_1,v__banked
                               movf     v___data_1,w,v__banked
                               return   
l_data_eeprom_write
                               movlb    3
                               movwf    v___data_3,v__banked
                               movf     v___offset_6,w,v__banked
                               movwf    v___offset_7,v__banked
                               movf     v___offset_6+1,w,v__banked
                               movwf    v___offset_7+1,v__banked
l__l239
                               btfsc    v_eecon1, 1,v__access ; eecon1_wr
                               goto     l__l239
l__l240
                               movf     v___tempoffset_2,w,v__banked
                               movwf    v_eeadr,v__access
                               bcf      v_eecon1, 6,v__access ; eecon1_cfgs
                               bcf      v_eecon1, 7,v__access ; eecon1_eepgd
                               movf     v___data_3,w,v__banked
                               movwf    v_eedata,v__access
                               bsf      v_eecon1, 2,v__access ; eecon1_wren
                               bcf      v____bitbucket_61, 0,v__banked ; gie_old
                               btfsc    v_intcon, 7,v__access ; intcon_gie
                               bsf      v____bitbucket_61, 0,v__banked ; gie_old
                               bcf      v_intcon, 7,v__access ; intcon_gie
                               movlw    85
                               movwf    v_eecon2,v__access
                               movlw    170
                               movwf    v_eecon2,v__access
                               bsf      v_eecon1, 1,v__access ; eecon1_wr
                               btfsc    v____bitbucket_61, 0,v__banked ; gie_old
                               goto     l__l1567
                               bcf      v_intcon, 7,v__access ; intcon_gie
                               goto     l__l1568
l__l1567
                               bsf      v_intcon, 7,v__access ; intcon_gie
l__l1568
                               bcf      v_eecon1, 2,v__access ; eecon1_wren
                               return   
l_data_eeprom_read_word
                               movf     v___offset_11,w,v__banked
                               movwf    v____temp_41,v__banked
                               movf     v___offset_11+1,w,v__banked
                               movwf    v____temp_41+1,v__banked
                               movf     v____temp_41,w,v__banked
                               movwf    v___offset_3,v__banked
                               movf     v____temp_41+1,w,v__banked
                               movwf    v___offset_3+1,v__banked
                               call     l_data_eeprom_read
                               movlb    3
                               movwf    v_tempbyte,v__banked
                               movlw    1
                               addwf    v___offset_11,w,v__banked
                               movwf    v____temp_41,v__banked
                               movlw    0
                               btfsc    v__status, v__c,v__access
                               movlw    1
                               addwf    v___offset_11+1,w,v__banked
                               movwf    v____temp_41+1,v__banked
                               movf     v____temp_41,w,v__banked
                               movwf    v___offset_3,v__banked
                               movf     v____temp_41+1,w,v__banked
                               movwf    v___offset_3+1,v__banked
                               call     l_data_eeprom_read
                               movlb    3
                               movwf    v_tempbyte+1,v__banked
                               return   
l_data_eeprom_write_word
                               movf     v___offset_15,w,v__banked
                               movwf    v____temp_42,v__banked
                               movf     v___offset_15+1,w,v__banked
                               movwf    v____temp_42+1,v__banked
                               movf     v____temp_42,w,v__banked
                               movwf    v___offset_6,v__banked
                               movf     v____temp_42+1,w,v__banked
                               movwf    v___offset_6+1,v__banked
                               movf     v___tempbyte_1,w,v__banked
                               call     l_data_eeprom_write
                               movlw    1
                               movlb    3
                               addwf    v___offset_15,w,v__banked
                               movwf    v____temp_42,v__banked
                               movlw    0
                               btfsc    v__status, v__c,v__access
                               movlw    1
                               addwf    v___offset_15+1,w,v__banked
                               movwf    v____temp_42+1,v__banked
                               movf     v____temp_42,w,v__banked
                               movwf    v___offset_6,v__banked
                               movf     v____temp_42+1,w,v__banked
                               movwf    v___offset_6+1,v__banked
                               movf     v___tempbyte_1+1,w,v__banked
                               goto     l_data_eeprom_write
; ../lib/i2c_software.jal
;   42 procedure i2c_initialize() is
l_i2c_initialize
;   43    i2c_scl              = low
                               bcf      v_latb, 1,v__access ; x114
;   44    i2c_sda              = low
                               bcf      v_latb, 0,v__access ; x115
;   45    i2c_scl_direction    = high
                               bsf      v_trisb, 1,v__access ; trisb_trisb1
;   46    i2c_sda_direction    = high
                               bsf      v_trisb, 0,v__access ; trisb_trisb0
;   53    i2c_start()
                               call     l_i2c_start
;   54    for 9 loop
                               movlb    3
                               clrf     v__floop9,v__banked
l__l281
;   55       _i2c_bit_out(1);
                               bsf      v____bitbucket_51, 0,v__banked ; x119
                               call     l__i2c_bit_out
;   56    end loop
                               movlb    3
                               incf     v__floop9,f,v__banked
                               movlw    9
                               subwf    v__floop9,w,v__banked
                               btfss    v__status, v__z,v__access
                               goto     l__l281
;   57    i2c_start()
                               call     l_i2c_start
;   58    i2c_stop()
                               goto     l_i2c_stop
;   60 end procedure
;   66 procedure i2c_start() is   
l_i2c_start
;   70    _i2c_wait()
                               call     l__i2c_wait
;   71    i2c_sda_direction = high       -- data high
                               bsf      v_trisb, 0,v__access ; trisb_trisb0
;   72    _i2c_wait() 
                               call     l__i2c_wait
;   73    i2c_scl_direction = high       -- clock high
                               bsf      v_trisb, 1,v__access ; trisb_trisb1
;   74    _i2c_wait()
                               call     l__i2c_wait
;   85       while i2c_scl == low loop 
l__l286
                               btfss    v_portb, 1,v__access ; pin_b1
;   86       end loop                     -- wait for slow slave
                               goto     l__l286
l__l287
;   89    i2c_sda_direction = low        -- data low
                               bcf      v_trisb, 0,v__access ; trisb_trisb0
;   90    _i2c_wait()
                               call     l__i2c_wait
;   91    i2c_scl_direction = low        -- clock low
                               bcf      v_trisb, 1,v__access ; trisb_trisb1
;   92    _i2c_wait()
                               goto     l__i2c_wait
;   93 end procedure
;  102 procedure i2c_restart() is       
l_i2c_restart
;  105    i2c_start()
                               goto     l_i2c_start
;  106 end procedure
;  112 procedure i2c_stop() is
l_i2c_stop
;  116    _i2c_wait()
                               call     l__i2c_wait
;  117    i2c_sda_direction   = low        -- data low
                               bcf      v_trisb, 0,v__access ; trisb_trisb0
;  118    _i2c_wait()
                               call     l__i2c_wait
;  119    i2c_scl_direction   = low        -- clock low
                               bcf      v_trisb, 1,v__access ; trisb_trisb1
;  120    _i2c_wait()
                               call     l__i2c_wait
;  121    i2c_scl_direction   = high       -- clock high
                               bsf      v_trisb, 1,v__access ; trisb_trisb1
;  122    _i2c_wait()       
                               call     l__i2c_wait
;  133       while i2c_scl == low loop 
l__l294
                               btfss    v_portb, 1,v__access ; pin_b1
;  134       end loop                     -- wait for slow slave
                               goto     l__l294
l__l295
;  137    i2c_sda_direction   = high       -- data high    
                               bsf      v_trisb, 0,v__access ; trisb_trisb0
;  138    _i2c_wait()
                               goto     l__i2c_wait
;  139 end procedure
;  146 function i2c_transmit_byte( byte in x ) return bit is
l_i2c_transmit_byte
                               movwf    v___x_117,v__banked
;  155    for 8 loop
                               clrf     v__floop10,v__banked
l__l300
;  156       _i2c_bit_out( b )
                               bcf      v____bitbucket_51, 0,v__banked ; x119
                               btfsc    v___x_117, 7,v__banked ; b
                               bsf      v____bitbucket_51, 0,v__banked ; x119
                               call     l__i2c_bit_out
;  157       x = x << 1   
                               bcf      v__status, v__c,v__access
                               movlb    3
                               rlcf     v___x_117,f,v__banked
;  158    end loop
                               incf     v__floop10,f,v__banked
                               movlw    8
                               subwf    v__floop10,w,v__banked
                               btfss    v__status, v__z,v__access
                               goto     l__l300
;  162    _i2c_wait()
                               call     l__i2c_wait
;  163    i2c_sda_direction    = high       -- data open
                               bsf      v_trisb, 0,v__access ; trisb_trisb0
;  164    _i2c_wait()
                               call     l__i2c_wait
;  165    i2c_scl_direction    = high       -- clock high
                               bsf      v_trisb, 1,v__access ; trisb_trisb1
;  166    _i2c_wait()               
                               call     l__i2c_wait
;  177       while i2c_scl == low loop 
l__l304
                               btfss    v_portb, 1,v__access ; pin_b1
;  178       end loop                     -- wait for slow slave
                               goto     l__l304
l__l305
;  182    r = ! i2c_sda
                               btfss    v_portb, 0,v__access ; pin_b0
                               goto     l__l1570
                               movlb    3
                               bcf      v____bitbucket_46, 0,v__banked ; r
                               goto     l__l1569
l__l1570
                               movlb    3
                               bsf      v____bitbucket_46, 0,v__banked ; r
l__l1569
;  183    _i2c_wait() 
                               call     l__i2c_wait
;  184    i2c_scl_direction    = low        -- clock low
                               bcf      v_trisb, 1,v__access ; trisb_trisb1
;  185    _i2c_wait()
                               call     l__i2c_wait
;  187    return r -- true = okay, false = no ack received
                               movlb    3
                               btfsc    v____bitbucket_46, 0,v__banked ; r
                               goto     l__l1571
                               movlb    0
                               bcf      v__pic_temp, 0,v__banked ; _pic_temp
                               return   
l__l1571
                               movlb    0
                               bsf      v__pic_temp, 0,v__banked ; _pic_temp
;  188 end function
                               return   
;  200 function i2c_receive_byte(bit in ack) return byte is
l_i2c_receive_byte
;  204    for 8 loop 
                               clrf     v__floop11,v__banked
l__l309
;  205       ret = ret << 1
                               bcf      v__status, v__c,v__access
                               rlcf     v_ret,f,v__banked
;  206       _i2c_bit_in( b )
                               call     l__i2c_bit_in
                               movlb    3
                               bcf      v_ret, 0,v__banked ; b1
                               btfsc    v____bitbucket_52, 0,v__banked ; x121
                               bsf      v_ret, 0,v__banked ; b1
;  207    end loop
                               incf     v__floop11,f,v__banked
                               movlw    8
                               subwf    v__floop11,w,v__banked
                               btfss    v__status, v__z,v__access
                               goto     l__l309
;  209    if (ack) then
                               btfss    v____bitbucket_45, 0,v__banked ; ack1
                               goto     l__l313
;  210       _i2c_bit_out( low ) -- ack
                               bcf      v____bitbucket_51, 0,v__banked ; x119
                               call     l__i2c_bit_out
;  211    else
                               goto     l__l312
l__l313
;  212       _i2c_bit_out( high ) -- nack
                               bsf      v____bitbucket_51, 0,v__banked ; x119
                               call     l__i2c_bit_out
;  213    end if
l__l312
;  220    return ret
                               movlb    3
                               movf     v_ret,w,v__banked
;  222 end function
                               return   
;  238 procedure  _i2c_wait() is
l__i2c_wait
;  250       delay_5us()
; ../lib/delay.jal
;   52   _usec_delay(5)
                               movlb    0
                               movlw    19
                               movwf    v__pic_temp,v__banked
l__l1573
                               decfsz   v__pic_temp,f,v__banked
                               goto     l__l1573
; ../lib/i2c_software.jal
;  250       delay_5us()
;  254 end procedure
                               return   
;  260 procedure _i2c_bit_out(bit in x) is
l__i2c_bit_out
;  262    i2c_sda_direction   = x          -- high data bit
                               btfsc    v____bitbucket_51, 0,v__banked ; x119
                               goto     l__l1574
                               bcf      v_trisb, 0,v__access ; trisb_trisb0
                               goto     l__l1575
l__l1574
                               bsf      v_trisb, 0,v__access ; trisb_trisb0
l__l1575
;  263    _i2c_wait()
                               call     l__i2c_wait
;  264    i2c_scl_direction  = high        -- clock high
                               bsf      v_trisb, 1,v__access ; trisb_trisb1
;  275       while i2c_scl == low loop 
l__l318
                               btfss    v_portb, 1,v__access ; pin_b1
;  276       end loop                     -- wait for slow slave
                               goto     l__l318
l__l319
;  279    _i2c_wait()
                               call     l__i2c_wait
;  280    i2c_scl_direction  = low         -- clock low
                               bcf      v_trisb, 1,v__access ; trisb_trisb1
;  281    _i2c_wait()
                               goto     l__i2c_wait
;  283 end procedure
;  289 procedure _i2c_bit_in(bit out x) is
l__i2c_bit_in
;  291    i2c_sda_direction   = high -- data open
                               bsf      v_trisb, 0,v__access ; trisb_trisb0
;  292    _i2c_wait()
                               call     l__i2c_wait
;  293    i2c_scl_direction  = high  -- clock high
                               bsf      v_trisb, 1,v__access ; trisb_trisb1
;  304       while i2c_scl == low loop 
l__l322
                               btfss    v_portb, 1,v__access ; pin_b1
;  305       end loop                     -- wait for slow slave
                               goto     l__l322
l__l323
;  308    _i2c_wait()
                               call     l__i2c_wait
;  309    x = i2c_sda                -- sample data
                               movlb    3
                               bcf      v____bitbucket_52, 0,v__banked ; x121
                               btfsc    v_portb, 0,v__access ; pin_b0
                               bsf      v____bitbucket_52, 0,v__banked ; x121
;  310    _i2c_wait()
                               call     l__i2c_wait
;  311    i2c_scl_direction  = low   -- clock low
                               bcf      v_trisb, 1,v__access ; trisb_trisb1
;  312    _i2c_wait()
                               goto     l__i2c_wait
;  313 end procedure
l__l269
; 18f4550_usb_hid_keyboard.jal
;  134 i2c_initialize()
                               call     l_i2c_initialize
; ../lib/eeprom_24lc256.jal
;   23 procedure ee_24lc256_read(byte in ic_address, word in mem_address, byte out data) is
                               goto     l__l327
l_ee_24lc256_read
                               movwf    v___ic_address_1,v__banked
;   30    address_high  = address_bytes[1]
                               movf     v_address_bytes+1,w,v__banked
                               movwf    v_address_high,v__banked
;   31    address_low = address_bytes[0]
                               movf     v_address_bytes,w,v__banked
                               movwf    v_address_low,v__banked
;   33    i2c_start()                                    -- send start bit
                               call     l_i2c_start
;   34    ack_ok = i2c_transmit_byte(ic_address)         -- transmit data & wait for ack
                               movlb    3
                               movf     v___ic_address_1,w,v__banked
                               call     l_i2c_transmit_byte
;   35    ack_ok = i2c_transmit_byte(address_high)       -- transmit data & wait for ack
                               movlb    3
                               movf     v_address_high,w,v__banked
                               call     l_i2c_transmit_byte
;   36    ack_ok = i2c_transmit_byte(address_low)        -- transmit data & wait for ack
                               movlb    3
                               movf     v_address_low,w,v__banked
                               call     l_i2c_transmit_byte
;   38    i2c_restart()                                    -- send start bit
                               call     l_i2c_start
;   39    ack_ok = i2c_transmit_byte(ic_address + 1)     -- transmit data & wait for ack
                               movlb    3
                               incf     v___ic_address_1,w,v__banked
                               movwf    v____temp_48,v__banked
                               movf     v____temp_48,w,v__banked
                               call     l_i2c_transmit_byte
;   40    data = i2c_receive_byte(0)                     -- nack (no ack)
                               movlb    3
                               bcf      v____bitbucket_45, 0,v__banked ; ack1
                               call     l_i2c_receive_byte
                               movlb    3
                               movwf    v___data_17,v__banked
;   41    i2c_stop()                                     -- send stop bit
                               call     l_i2c_stop
;   42 end procedure
                               movlb    3
                               movf     v___data_17,w,v__banked
                               return   
;   47 procedure ee_24lc256_write(byte in ic_address, word in mem_address, byte in data) is
l_ee_24lc256_write
                               movwf    v___ic_address_3,v__banked
;   55    address_high  = address_bytes[1]
                               movf     v___address_bytes_1+1,w,v__banked
                               movwf    v___address_high_1,v__banked
;   56    address_low = address_bytes[0]
                               movf     v___address_bytes_1,w,v__banked
                               movwf    v___address_low_1,v__banked
;   58    i2c_start()                              -- send start bit
                               call     l_i2c_start
;   59    ack_ok = i2c_transmit_byte(ic_address)    -- transmit data & wait for ack
                               movlb    3
                               movf     v___ic_address_3,w,v__banked
                               call     l_i2c_transmit_byte
;   60    ack_ok = i2c_transmit_byte(address_high) -- transmit data & wait for ack
                               movlb    3
                               movf     v___address_high_1,w,v__banked
                               call     l_i2c_transmit_byte
;   61    ack_ok = i2c_transmit_byte(address_low)  -- transmit data & wait for ack
                               movlb    3
                               movf     v___address_low_1,w,v__banked
                               call     l_i2c_transmit_byte
;   62    ack_ok = i2c_transmit_byte(data)         -- transmit data & wait for ack
                               movlb    3
                               movf     v___data_19,w,v__banked
                               call     l_i2c_transmit_byte
;   63    i2c_stop()                               -- send stop bit
                               call     l_i2c_stop
;   65    _usec_delay(5_000)                      -- datasheet says writes take 5ms
                               movlb    0
                               movlw    106
                               movwf    v__pic_temp,v__banked
l__l1576
                               movlw    187
                               movwf    v__pic_temp+1,v__banked
l__l1577
                               decfsz   v__pic_temp+1,f,v__banked
                               goto     l__l1577
                               decfsz   v__pic_temp,f,v__banked
                               goto     l__l1576
                               nop      
;   66 end procedure
                               return   
l__l327
; ../lib/usb_defs.jal
;  148 var byte usb_state = USB_STATE_POWERED
                               movlb    0
                               clrf     v_usb_state,v__banked
; ../lib/usb_keyboard.jal
;  358 end if
                               goto     l__l422
; ../lib/usb_drv_core.jal
;   28 procedure _usb_copy_array_to_ram(word in dst, byte in data[], byte in num_bytes ) is 
l__usb_copy_array_to_ram
                               movlb    3
                               movwf    v___num_bytes_1,v__banked
;   33 	FSR1L = dst_ptr[0]
                               movf     v_dst_ptr,w,v__banked
                               movwf    v_fsr1l,v__access
;   34 	FSR1H = dst_ptr[1]
                               movf     v_dst_ptr+1,w,v__banked
                               movwf    v_fsr1h,v__access
;   36 	for num_bytes using index loop
                               movf     v___num_bytes_1,w,v__banked
                               movwf    v__floop12,v__banked
                               clrf     v_index,v__banked
                               goto     l__l341
l__l340
;   37 		POSTINC1 = data[index]
                               movf     v___data_22,w,v__banked
                               addwf    v_index,w,v__banked
                               movlb    0
                               movwf    v__pic_pointer,v__banked
                               movlw    0
                               movwf    v__pic_accum,v__access
                               movlb    3
                               movf     v___data_22+1,w,v__banked
                               addwfc   v__pic_accum,w,v__access
                               movlb    0
                               movwf    v__pic_pointer+1,v__banked
                               movlb    3
                               movf     v___data_22+2,w,v__banked
                               addwfc   v__pic_accum,w,v__access
                               movlb    0
                               movwf    v__pic_pointer+2,v__banked
                               call     l__pic_pointer_read
                               movwf    v_postinc1,v__access
;   38 	end loop
                               movlb    3
                               incf     v_index,f,v__banked
l__l341
                               movf     v_index,w,v__banked
                               subwf    v__floop12,w,v__banked
                               btfss    v__status, v__z,v__access
                               goto     l__l340
;   39 end procedure
                               return   
;   44 procedure usb_send_data_chunk() is
l_usb_send_data_chunk
;   48 	if ( own_bit ) then
                               movlb    4
                               btfsc    v_usb_bd0in_stat, 7,v__banked ; own_bit
;   53 	else
                               return   
l__l346
;   56 		if ( usb_delivery_bytes_to_send > usb_delivery_bytes_max_send ) then
                               movlb    0
                               movf     v_usb_delivery_bytes_to_send,w,v__banked
                               subwf    v_usb_delivery_bytes_max_send,w,v__banked
                               btfsc    v__status, v__z,v__access
                               goto     l__l349
                               btfsc    v__status, v__c,v__access
                               goto     l__l349
;   62 			usb_delivery_bytes_to_send = usb_delivery_bytes_max_send
                               movf     v_usb_delivery_bytes_max_send,w,v__banked
                               movwf    v_usb_delivery_bytes_to_send,v__banked
;   63 		end if
l__l349
;   65 		byte_cnt = usb_delivery_bytes_to_send - usb_delivery_bytes_sent
                               bsf      v__status, v__c,v__access
                               movf     v_usb_delivery_bytes_to_send,w,v__banked
                               subfwb   v_usb_delivery_bytes_sent,w,v__banked
                               movlb    3
                               movwf    v_byte_cnt,v__banked
;   67 		if ( byte_cnt > usb_delivery_buffer_size ) then
                               movf     v_byte_cnt,w,v__banked
                               movlb    0
                               subwf    v_usb_delivery_buffer_size,w,v__banked
                               btfsc    v__status, v__z,v__access
                               goto     l__l352
                               btfsc    v__status, v__c,v__access
                               goto     l__l352
;   68 			byte_cnt = usb_delivery_buffer_size
                               movf     v_usb_delivery_buffer_size,w,v__banked
                               movlb    3
                               movwf    v_byte_cnt,v__banked
;   69 		end if
l__l352
;   87 		usb_bd0in_addr = USB_IN_DELIVERY_BUFFER_LOC + usb_delivery_bytes_sent
                               movlw    120
                               movlb    0
                               addwf    v_usb_delivery_bytes_sent,w,v__banked
                               movlb    4
                               movwf    v_usb_bd0in_addr,v__banked
                               movlw    0
                               movwf    v__pic_accum,v__access
                               movlw    4
                               addwfc   v__pic_accum,w,v__access
                               movwf    v_usb_bd0in_addr+1,v__banked
;   88 		usb_bd0in_cnt = byte_cnt
                               movlb    3
                               movf     v_byte_cnt,w,v__banked
                               movlb    4
                               movwf    v_usb_bd0in_cnt,v__banked
;   91 		if ( dts_bit  ) then
                               btfss    v_usb_bd0in_stat, 6,v__banked ; dts_bit
                               goto     l__l355
;   95 			usb_bd0in_stat = 0b_1000_1000
                               movlw    136
                               movwf    v_usb_bd0in_stat,v__banked
;   96 		else
                               goto     l__l354
l__l355
;  100 			usb_bd0in_stat = 0b_1100_1000
                               movlw    200
                               movwf    v_usb_bd0in_stat,v__banked
;  101 		end if
l__l354
;  103 		usb_delivery_bytes_sent = usb_delivery_bytes_sent + byte_cnt
                               movlb    3
                               movf     v_byte_cnt,w,v__banked
                               movlb    0
                               addwf    v_usb_delivery_bytes_sent,f,v__banked
;  105 		if ( usb_delivery_bytes_sent == usb_delivery_bytes_to_send )  then
                               movf     v_usb_delivery_bytes_sent,w,v__banked
                               subwf    v_usb_delivery_bytes_to_send,w,v__banked
;  111 	end if
l__l345
;  112 end procedure
                               return   
;  118 procedure usb_send_empty_data_pkt() is
l_usb_send_empty_data_pkt
;  120 	usb_delivery_buffer_size = USB_EP0_IN_SIZE
                               movlw    8
                               movwf    v_usb_delivery_buffer_size,v__banked
;  124 	usb_delivery_bytes_sent = 0
                               clrf     v_usb_delivery_bytes_sent,v__banked
;  125 	usb_delivery_bytes_to_send = 0
                               clrf     v_usb_delivery_bytes_to_send,v__banked
;  126 	usb_delivery_bytes_max_send = 0
                               clrf     v_usb_delivery_bytes_max_send,v__banked
;  131 	dts_bit = low
                               movlb    4
                               bcf      v_usb_bd0in_stat, 6,v__banked ; dts_bit1
;  133 	usb_send_data_chunk()
                               goto     l_usb_send_data_chunk
;  135 end procedure
;  150 procedure usb_send_one_byte(byte in data) is
l_usb_send_one_byte
                               movlb    3
                               movwf    v___data_24,v__banked
;  151 	usb_delivery_buffer[0] = data
                               movf     v___data_24,w,v__banked
                               movlb    4
                               movwf    v_usb_delivery_buffer,v__banked
;  152 	usb_delivery_buffer_size = USB_EP0_IN_SIZE
                               movlw    8
                               movlb    0
                               movwf    v_usb_delivery_buffer_size,v__banked
;  153 	usb_delivery_bytes_sent = 0
                               clrf     v_usb_delivery_bytes_sent,v__banked
;  154 	usb_delivery_bytes_to_send = 1
                               movlw    1
                               movwf    v_usb_delivery_bytes_to_send,v__banked
;  155 	usb_delivery_bytes_max_send = 1 -- AF from 0 to 1??????
                               movlw    1
                               movwf    v_usb_delivery_bytes_max_send,v__banked
;  159 	dts_bit = low
                               movlb    4
                               bcf      v_usb_bd0in_stat, 6,v__banked ; dts_bit2
;  161 	usb_send_data_chunk()
                               goto     l_usb_send_data_chunk
;  162 end procedure
;  172 procedure usb_send_data(byte in endpoint, byte in data[], byte in byte_cnt, bit in is_new_sequence ) is
l_usb_send_data
                               movwf    v___endpoint_1,v__banked
;  187 	case endpoint of
;  188 		0:
                               movf     v___endpoint_1,w,v__banked
                               btfss    v__status, v__z,v__access
                               goto     l__l371
;  189 		block
;  190 			_usb_copy_array_to_ram( USB_EP0_IN_ADDR, data, byte_cnt )
                               movlw    24
                               movwf    v___dst_1,v__banked
                               movlw    4
                               movwf    v___dst_1+1,v__banked
                               movf     v___data_26,w,v__banked
                               movwf    v___data_22,v__banked
                               movf     v___data_26+1,w,v__banked
                               movwf    v___data_22+1,v__banked
                               movf     v___data_26+2,w,v__banked
                               movwf    v___data_22+2,v__banked
                               movf     v___byte_cnt_2,w,v__banked
                               call     l__usb_copy_array_to_ram
;  191 			usb_bd0in_addr = USB_EP0_IN_ADDR
                               movlw    24
                               movlb    4
                               movwf    v_usb_bd0in_addr,v__banked
                               movlw    4
                               movwf    v_usb_bd0in_addr+1,v__banked
;  194 			if is_new_sequence then
                               movlb    3
                               btfss    v____bitbucket_37, 0,v__banked ; is_new_sequence1
                               goto     l__l374
;  196 				dts_bit = low
                               movlb    4
                               bcf      v_usb_bd0in_stat, 6,v__banked ; dts_bit3
;  197 			end if
l__l374
;  205 			if ( dts_bit  ) then
                               movlb    4
                               btfss    v_usb_bd0in_stat, 6,v__banked ; dts_bit3
                               goto     l__l377
;  209 				usb_bd0in_stat = 0b_1000_1000
                               movlw    136
                               movwf    v_usb_bd0in_stat,v__banked
;  210 			else
                               return   
l__l377
;  214 				usb_bd0in_stat = 0b_1100_1000
                               movlw    200
                               movwf    v_usb_bd0in_stat,v__banked
;  215 			end if		
;  216 		end block
                               return   
l__l371
;  218 		1:
                               movlw    1
                               subwf    v___endpoint_1,w,v__banked
                               btfss    v__status, v__z,v__access
                               goto     l__l381
;  219 		block
;  221 				_usb_copy_array_to_ram( USB_EP1_IN_ADDR, data, byte_cnt )
                               movlw    40
                               movwf    v___dst_1,v__banked
                               movlw    4
                               movwf    v___dst_1+1,v__banked
                               movf     v___data_26,w,v__banked
                               movwf    v___data_22,v__banked
                               movf     v___data_26+1,w,v__banked
                               movwf    v___data_22+1,v__banked
                               movf     v___data_26+2,w,v__banked
                               movwf    v___data_22+2,v__banked
                               movf     v___byte_cnt_2,w,v__banked
                               call     l__usb_copy_array_to_ram
;  222 				usb_bd1in_addr = USB_EP1_IN_ADDR
                               movlw    40
                               movlb    4
                               movwf    v_usb_bd1in_addr,v__banked
                               movlw    4
                               movwf    v_usb_bd1in_addr+1,v__banked
;  224 				usb_bd1in_cnt = byte_cnt
                               movlb    3
                               movf     v___byte_cnt_2,w,v__banked
                               movlb    4
                               movwf    v_usb_bd1in_cnt,v__banked
;  226 				if is_new_sequence then
                               movlb    3
                               btfss    v____bitbucket_37, 0,v__banked ; is_new_sequence1
                               goto     l__l386
;  227 					dts_bit = low
                               movlb    4
                               bcf      v_usb_bd1in_stat, 6,v__banked ; dts_bit4
;  228 				end if
l__l386
;  229 				if ( dts_bit  ) then
                               movlb    4
                               btfss    v_usb_bd1in_stat, 6,v__banked ; dts_bit4
                               goto     l__l388
;  230 					usb_bd1in_stat = 0b_1000_1000
                               movlw    136
                               movwf    v_usb_bd1in_stat,v__banked
;  231 				else
                               return   
l__l388
;  232 					usb_bd1in_stat = 0b_1100_1000
                               movlw    200
                               movwf    v_usb_bd1in_stat,v__banked
;  233 				end if		
;  234 			end if
                               return   
;  235 		end block
l__l381
;  236 		2:
                               movlw    2
                               subwf    v___endpoint_1,w,v__banked
                               btfsc    v__status, v__z,v__access
;  251 		end block		
                               return   
l__l389
;  252 		3:
                               movlw    3
                               subwf    v___endpoint_1,w,v__banked
;  267 		end block
;  275 		end block
l__l380
;  278 end procedure
                               return   
;  388 procedure usb_stall_ep0() is
l_usb_stall_ep0
;  399 	usb_bd0out_stat = usb_bd0out_stat | 0b_1000_0100
                               movlw    132
                               movlb    4
                               iorwf    v_usb_bd0out_stat,f,v__banked
;  400 end procedure
                               return   
;  403 procedure usb_prime_ep0_out() is
l_usb_prime_ep0_out
;  405 	usb_bd0out_cnt = USB_EP0_OUT_SIZE
                               movlw    8
                               movlb    4
                               movwf    v_usb_bd0out_cnt,v__banked
;  406 	usb_bd0out_addr = USB_EP0_OUT_ADDR
                               movlw    16
                               movwf    v_usb_bd0out_addr,v__banked
                               movlw    4
                               movwf    v_usb_bd0out_addr+1,v__banked
;  409 	if ( usb_control_mode == USB_CM_CTRL_READ_DATA_STAGE ) then
                               movlw    3
                               movlb    0
                               subwf    v_usb_control_mode,w,v__banked
                               btfss    v__status, v__z,v__access
                               goto     l__l419
;  410 		new_value = 0x8C
                               movlw    140
                               movlb    3
                               movwf    v_new_value,v__banked
;  417 		usb_bd0in_stat = 0x00
                               movlb    4
                               clrf     v_usb_bd0in_stat,v__banked
;  418 	else
                               goto     l__l418
l__l419
;  420 		new_value = 0b_1100_1000	
                               movlw    200
                               movlb    3
                               movwf    v_new_value,v__banked
;  421 	end if
l__l418
;  431 	usb_bd0out_stat = new_value		
                               movlb    3
                               movf     v_new_value,w,v__banked
                               movlb    4
                               movwf    v_usb_bd0out_stat,v__banked
;  432 end procedure
                               return   
;  434 procedure usb_prime_epx_out( byte in end_point, byte in size ) is 
l_usb_prime_epx_out
                               movwf    v___end_point_1,v__banked
;  435 	var byte idx = end_point * 8
                               bcf      v__status, v__c,v__access
                               rlcf     v___end_point_1,w,v__banked
                               movwf    v___idx_1,v__banked
                               bcf      v__status, v__c,v__access
                               rlcf     v___idx_1,f,v__banked
                               bcf      v__status, v__c,v__access
                               rlcf     v___idx_1,f,v__banked
;  437 	usb_bd_array[ idx + 1 ] = size
                               incf     v___idx_1,w,v__banked
                               movwf    v____temp_51,v__banked
                               lfsr     0,v_usb_bd_array
                               movf     v____temp_51,w,v__banked
                               addwf    v__fsr0l,f,v__access
                               movf     v___size_1,w,v__banked
                               movwf    v__ind,v__access
;  439 	usb_bd_array[ idx  ] = 0x80 				
                               lfsr     0,v_usb_bd_array
                               movf     v___idx_1,w,v__banked
                               addwf    v__fsr0l,f,v__access
                               movlw    128
                               movwf    v__ind,v__access
;  441 end procedure
                               return   
l__l422
; ../lib/usb_keyboard.jal
;  391 var volatile bit _usb_hid_can_tx = true
                               movlb    1
                               bsf      v__bitbucket, 0,v__banked ; _usb_hid_can_tx
;  404 procedure usb_handle_class_request_callback() is
                               goto     l__l767
l_usb_handle_class_request_callback
;  407     var byte req01 = usb_sdp_request
                               movlb    4
                               movf     v_usb_sdp_request,w,v__banked
                               movlb    3
                               movwf    v_req01,v__banked
;  408     var word len = usb_sdp_length
                               movlb    4
                               movf     v_usb_sdp_length,w,v__banked
                               movlb    3
                               movwf    v_len,v__banked
                               movlb    4
                               movf     v_usb_sdp_length+1,w,v__banked
                               movlb    3
                               movwf    v_len+1,v__banked
;  426 	case (req01) of
;  429 		USB_HCR_GET_REPORT:
                               movlw    1
                               subwf    v_req01,w,v__banked
                               btfsc    v__status, v__z,v__access
;  435 		end block
                               return   
l__l427
;  437 		USB_HCR_GET_IDLE:
                               movlw    2
                               subwf    v_req01,w,v__banked
                               btfsc    v__status, v__z,v__access
;  443 		end block
                               return   
l__l431
;  445 		USB_HCR_GET_PROTOCOL:
                               movlw    3
                               subwf    v_req01,w,v__banked
                               btfsc    v__status, v__z,v__access
;  451 		end block
                               return   
l__l434
;  453 		USB_HCR_SET_REPORT:
                               movlw    9
                               subwf    v_req01,w,v__banked
                               btfss    v__status, v__z,v__access
                               goto     l__l437
;  454 		block
;  460          if ( len > 0 ) then
                               movf     v_len,w,v__banked
                               iorwf    v_len+1,w,v__banked
                               btfsc    v__status, v__z,v__access
                               goto     l__l430
;  461             usb_control_mode = USB_CM_CTRL_WRITE_DATA_STAGE_CLASS
                               movlw    2
                               movlb    0
                               movwf    v_usb_control_mode,v__banked
;  462          end if
;  463 		end block
                               return   
l__l437
;  465 		USB_HCR_SET_IDLE:
                               movlw    10
                               subwf    v_req01,w,v__banked
                               btfsc    v__status, v__z,v__access
;  471 		end block
                               return   
l__l442
;  473 		USB_HCR_SET_PROTOCOL:
                               movlw    11
                               subwf    v_req01,w,v__banked
;  479 		end block
;  487 		end block
l__l430
;  490 end procedure
                               return   
;  494 procedure usb_handle_class_ctrl_write_callback() is
l_usb_handle_class_ctrl_write_callback
;  496     var byte req01 = usb_sdp_request
                               movlb    4
                               movf     v_usb_sdp_request,w,v__banked
                               movlb    3
                               movwf    v___req01_1,v__banked
;  506 	case (req01) of
;  507 		USB_HCR_SET_REPORT:
                               movlw    9
                               subwf    v___req01_1,w,v__banked
                               btfss    v__status, v__z,v__access
                               goto     l__l454
;  508 		block
;  511 			_usb_keyboard_led_status = bd0_out_buffer[0]
;  525          usb_control_mode = USB_CM_CTRL_WRITE_SENDING_STATUS
                               movlw    6
                               movlb    0
                               movwf    v_usb_control_mode,v__banked
;  526          usb_send_status_ack()
; ../lib/usb_drv_core.jal
;  143 	usb_send_empty_data_pkt()
                               goto     l_usb_send_empty_data_pkt
; ../lib/usb_keyboard.jal
;  526          usb_send_status_ack()
;  528 		end block
l__l454
;  540 end procedure
                               return   
;  542 procedure usb_handle_class_ctrl_read_callback() is
l_usb_handle_class_ctrl_read_callback
;  560 end procedure
                               return   
; ../lib/usb_drv.jal
;   59 procedure _usb_handle_standard_request() is
l__usb_handle_standard_request
;   60 	var volatile byte request = usb_sdp_request
                               movlb    4
                               movf     v_usb_sdp_request,w,v__banked
                               movlb    0
                               movwf    v_request,v__banked
;   64 	case request of
;   66 		USB_REQUEST_GET_DESCRIPTOR:
                               movlw    6
                               subwf    v_request,w,v__banked
                               btfss    v__status, v__z,v__access
                               goto     l__l479
;   67 		block
;   74 			var byte descriptor_type = wbt_value[1] -- high byte is descriptor
                               movlb    4
                               movf     v_wbt_value+1,w,v__banked
                               movlb    3
                               movwf    v_descriptor_type,v__banked
;   75 			var byte descriptor_num  = wbt_value[0] -- low byte is particular descriptor
                               movlb    4
                               movf     v_wbt_value,w,v__banked
                               movlb    3
                               movwf    v_descriptor_num,v__banked
;   77 			usb_delivery_bytes_to_send = 0 
                               movlb    0
                               clrf     v_usb_delivery_bytes_to_send,v__banked
;   83 			case descriptor_type of
;   84 				USB_DT_DEVICE:
                               movlw    1
                               movlb    3
                               subwf    v_descriptor_type,w,v__banked
                               btfss    v__status, v__z,v__access
                               goto     l__l483
;   85 				block
;   89 					usb_delivery_bytes_to_send = count( USB_DEVICE_DESCRIPTOR )
                               movlw    18
                               movlb    0
                               movwf    v_usb_delivery_bytes_to_send,v__banked
;   91 					_usb_copy_array_to_ram( USB_IN_DELIVERY_BUFFER_LOC, USB_DEVICE_DESCRIPTOR, usb_delivery_bytes_to_send )
                               movlw    120
                               movlb    3
                               movwf    v___dst_1,v__banked
                               movlw    4
                               movwf    v___dst_1+1,v__banked
                               movlw    l__data_usb_device_descriptor
                               movwf    v___data_22,v__banked
                               movlw    HIGH l__data_usb_device_descriptor
                               movwf    v___data_22+1,v__banked
                               movlw    UPPER l__data_usb_device_descriptor
                               iorlw    64
                               movwf    v___data_22+2,v__banked
                               movlb    0
                               movf     v_usb_delivery_bytes_to_send,w,v__banked
                               call     l__usb_copy_array_to_ram
;   92 				end block	
                               goto     l__l485
l__l483
;   94 				USB_DT_CONFIGURATION:
                               movlw    2
                               subwf    v_descriptor_type,w,v__banked
                               btfss    v__status, v__z,v__access
                               goto     l__l486
;   95 				block	
;  100 					usb_delivery_bytes_to_send = count( USB_CONFIGURATION_DESCRIPTOR )
                               movlw    34
                               movlb    0
                               movwf    v_usb_delivery_bytes_to_send,v__banked
;  102 					_usb_copy_array_to_ram( USB_IN_DELIVERY_BUFFER_LOC, USB_CONFIGURATION_DESCRIPTOR, usb_delivery_bytes_to_send )				
                               movlw    120
                               movlb    3
                               movwf    v___dst_1,v__banked
                               movlw    4
                               movwf    v___dst_1+1,v__banked
                               movlw    l__data_usb_configuration_descriptor
                               movwf    v___data_22,v__banked
                               movlw    HIGH l__data_usb_configuration_descriptor
                               movwf    v___data_22+1,v__banked
                               movlw    UPPER l__data_usb_configuration_descriptor
                               iorlw    64
                               movwf    v___data_22+2,v__banked
                               movlb    0
                               movf     v_usb_delivery_bytes_to_send,w,v__banked
                               call     l__usb_copy_array_to_ram
;  103 				end block
                               goto     l__l485
l__l486
;  105 				USB_DT_STRING:
                               movlw    3
                               subwf    v_descriptor_type,w,v__banked
                               btfss    v__status, v__z,v__access
                               goto     l__l489
;  106 				block			
;  116 						if (descriptor_num == 0 ) then
                               movf     v_descriptor_num,w,v__banked
                               btfss    v__status, v__z,v__access
                               goto     l__l492
;  117 							usb_delivery_bytes_to_send = count( USB_STRING0 )
                               movlw    4
                               movlb    0
                               movwf    v_usb_delivery_bytes_to_send,v__banked
;  118 							_usb_copy_array_to_ram( USB_IN_DELIVERY_BUFFER_LOC, USB_STRING0, usb_delivery_bytes_to_send )
                               movlw    120
                               movlb    3
                               movwf    v___dst_1,v__banked
                               movlw    4
                               movwf    v___dst_1+1,v__banked
                               movlw    l__data_usb_string0
                               movwf    v___data_22,v__banked
                               movlw    HIGH l__data_usb_string0
                               movwf    v___data_22+1,v__banked
                               movlw    UPPER l__data_usb_string0
                               iorlw    64
                               movwf    v___data_22+2,v__banked
                               movlb    0
                               movf     v_usb_delivery_bytes_to_send,w,v__banked
                               call     l__usb_copy_array_to_ram
;  119 						end if
;  120 					end if
l__l492
;  122 						if (descriptor_num == 1 ) then
                               movlw    1
                               movlb    3
                               subwf    v_descriptor_num,w,v__banked
                               btfss    v__status, v__z,v__access
                               goto     l__l496
;  123 							usb_delivery_bytes_to_send = count( USB_STRING1 )
                               movlw    54
                               movlb    0
                               movwf    v_usb_delivery_bytes_to_send,v__banked
;  124 							_usb_copy_array_to_ram( USB_IN_DELIVERY_BUFFER_LOC, USB_STRING1, usb_delivery_bytes_to_send )
                               movlw    120
                               movlb    3
                               movwf    v___dst_1,v__banked
                               movlw    4
                               movwf    v___dst_1+1,v__banked
                               movlw    l__data_usb_string1
                               movwf    v___data_22,v__banked
                               movlw    HIGH l__data_usb_string1
                               movwf    v___data_22+1,v__banked
                               movlw    UPPER l__data_usb_string1
                               iorlw    64
                               movwf    v___data_22+2,v__banked
                               movlb    0
                               movf     v_usb_delivery_bytes_to_send,w,v__banked
                               call     l__usb_copy_array_to_ram
;  125 						end if
;  126 					end if					
l__l496
;  128 						if (descriptor_num == 2 ) then
                               movlw    2
                               movlb    3
                               subwf    v_descriptor_num,w,v__banked
                               btfss    v__status, v__z,v__access
                               goto     l__l485
;  129 							usb_delivery_bytes_to_send = count( USB_STRING2 )
                               movlw    42
                               movlb    0
                               movwf    v_usb_delivery_bytes_to_send,v__banked
;  130 							_usb_copy_array_to_ram( USB_IN_DELIVERY_BUFFER_LOC, USB_STRING2, usb_delivery_bytes_to_send )
                               movlw    120
                               movlb    3
                               movwf    v___dst_1,v__banked
                               movlw    4
                               movwf    v___dst_1+1,v__banked
                               movlw    l__data_usb_string2
                               movwf    v___data_22,v__banked
                               movlw    HIGH l__data_usb_string2
                               movwf    v___data_22+1,v__banked
                               movlw    UPPER l__data_usb_string2
                               iorlw    64
                               movwf    v___data_22+2,v__banked
                               movlb    0
                               movf     v_usb_delivery_bytes_to_send,w,v__banked
                               call     l__usb_copy_array_to_ram
;  131 						end if
;  132 					end if				
                               goto     l__l485
;  145 				end block
l__l489
;  151 				USB_DT_HID_REPORT:
                               movlw    34
                               subwf    v_descriptor_type,w,v__banked
                               btfss    v__status, v__z,v__access
                               goto     l__l506
;  152 				block
;  159 						usb_delivery_bytes_to_send = count( USB_HID_REPORT1 )
                               movlw    63
                               movlb    0
                               movwf    v_usb_delivery_bytes_to_send,v__banked
;  160 						_usb_copy_array_to_ram( USB_IN_DELIVERY_BUFFER_LOC, USB_HID_REPORT1, usb_delivery_bytes_to_send )					
                               movlw    120
                               movlb    3
                               movwf    v___dst_1,v__banked
                               movlw    4
                               movwf    v___dst_1+1,v__banked
                               movlw    l__data_usb_hid_report1
                               movwf    v___data_22,v__banked
                               movlw    HIGH l__data_usb_hid_report1
                               movwf    v___data_22+1,v__banked
                               movlw    UPPER l__data_usb_hid_report1
                               iorlw    64
                               movwf    v___data_22+2,v__banked
                               movlb    0
                               movf     v_usb_delivery_bytes_to_send,w,v__banked
                               call     l__usb_copy_array_to_ram
;  162 				end block
l__l506
;  171 				end block
l__l485
;  177 			if ( usb_delivery_bytes_to_send > 0 ) then
                               movlb    0
                               movf     v_usb_delivery_bytes_to_send,w,v__banked
                               btfsc    v__status, v__z,v__access
                               goto     l__l515
;  180 				usb_delivery_buffer_size = USB_EP0_IN_SIZE
                               movlw    8
                               movwf    v_usb_delivery_buffer_size,v__banked
;  182 				if ( wbt_length[1] == 0  ) then
                               movlb    4
                               movf     v_wbt_length+1,w,v__banked
                               btfss    v__status, v__z,v__access
                               goto     l__l517
;  183 					usb_delivery_bytes_max_send = wbt_length[0]
                               movf     v_wbt_length,w,v__banked
                               movlb    0
                               movwf    v_usb_delivery_bytes_max_send,v__banked
;  184 				else
                               goto     l__l516
l__l517
;  185 					usb_delivery_bytes_max_send = 0xFF
                               movlw    255
                               movlb    0
                               movwf    v_usb_delivery_bytes_max_send,v__banked
;  186 				end if
l__l516
;  189 				usb_control_mode = USB_CM_CTRL_READ_DATA_STAGE
                               movlw    3
                               movwf    v_usb_control_mode,v__banked
;  190 				usb_delivery_bytes_sent = 0
                               clrf     v_usb_delivery_bytes_sent,v__banked
;  192 				dts_bit = low				
                               movlb    4
                               bcf      v_usb_bd0in_stat, 6,v__banked ; dts_bit5
;  195 				usb_send_data_chunk()
                               goto     l_usb_send_data_chunk
;  197 			else
l__l515
;  202 				usb_stall_ep0();
                               goto     l_usb_stall_ep0
;  203 			end if						
;  204 		end block
l__l479
;  206 		USB_REQUEST_SET_ADDRESS:
                               movlw    5
                               subwf    v_request,w,v__banked
                               btfss    v__status, v__z,v__access
                               goto     l__l520
;  207 		block
;  208 			usb_address = wbt_value[0]
                               movlb    4
                               movf     v_wbt_value,w,v__banked
                               movlb    0
                               movwf    v_usb_address,v__banked
;  214 			usb_status = USB_STATUS_SET_ADDRESS
                               movlw    1
                               movwf    v_usb_status,v__banked
;  217 			usb_send_status_ack()
; ../lib/usb_drv_core.jal
;  143 	usb_send_empty_data_pkt()
                               call     l_usb_send_empty_data_pkt
; ../lib/usb_drv.jal
;  217 			usb_send_status_ack()
;  218 			usb_control_mode = USB_CM_CTRL_WRITE_SENDING_STATUS
                               movlw    6
                               movlb    0
                               movwf    v_usb_control_mode,v__banked
;  219 		end block
                               return   
l__l520
;  221 		USB_REQUEST_SET_CONFIGURATION:
                               movlw    9
                               subwf    v_request,w,v__banked
                               btfss    v__status, v__z,v__access
                               goto     l__l524
;  222 		block
;  229 			usb_control_mode = USB_CM_CTRL_WRITE_SENDING_STATUS
                               movlw    6
                               movwf    v_usb_control_mode,v__banked
;  230 			usb_send_status_ack()
; ../lib/usb_drv_core.jal
;  143 	usb_send_empty_data_pkt()
                               call     l_usb_send_empty_data_pkt
; ../lib/usb_drv.jal
;  230 			usb_send_status_ack()
;  232 			usb_state = USB_STATE_CONFIGURED
                               movlw    3
                               movlb    0
                               movwf    v_usb_state,v__banked
;  235 			usb_configure_endpoints();
; ../lib/usb_drv_core.jal
;  293 		EP1HSHK = high -- EP handshaking on
                               bsf      v_uep1, 4,v__access ; ep1hshk
;  296 			EP1OUTEN = high -- EP OUT enabled
                               bsf      v_uep1, 2,v__access ; ep1outen
;  302 			EP1INEN = high -- EP IN enabled
                               bsf      v_uep1, 1,v__access ; ep1inen
;  307 		EP1CONDIS = high -- control transfers off
                               bsf      v_uep1, 3,v__access ; ep1condis
;  312 			usb_bd1in_stat  = 0b01000000
                               movlw    64
                               movlb    4
                               movwf    v_usb_bd1in_stat,v__banked
;  317 			usb_bd1out_cnt  = USB_EP1_OUT_SIZE;
                               movlw    8
                               movwf    v_usb_bd1out_cnt,v__banked
;  318 			usb_bd1out_addr = USB_EP1_OUT_ADDR;
                               movlw    32
                               movwf    v_usb_bd1out_addr,v__banked
                               movlw    4
                               movwf    v_usb_bd1out_addr+1,v__banked
;  320 			usb_bd1out_stat = 0b10000000 
                               movlw    128
                               movwf    v_usb_bd1out_stat,v__banked
;  321 		end if
                               return   
; ../lib/usb_drv.jal
;  241 		end block
l__l524
;  243 		USB_REQUEST_GET_INTERFACE:
                               movlw    10
                               subwf    v_request,w,v__banked
                               btfss    v__status, v__z,v__access
                               goto     l__l543
;  244 		block
;  249 			usb_control_mode = USB_CM_CTRL_READ_DATA_STAGE
                               movlw    3
                               movwf    v_usb_control_mode,v__banked
;  250 			usb_send_one_byte( 1 )
                               movlw    1
                               goto     l_usb_send_one_byte
;  251 		end block
l__l543
;  253 		USB_REQUEST_GET_STATUS:
                               movf     v_request,w,v__banked
                               btfss    v__status, v__z,v__access
                               goto     l__l546
;  254 		block
;  262 			usb_send_one_byte(0)
                               movlw    0
                               goto     l_usb_send_one_byte
;  288 		end block
l__l546
;  298 		end block
l__l519
;  302 end procedure	
                               return   
;  312 procedure _usb_handle_transaction() is
l__usb_handle_transaction
;  317 	end_point = USTAT >> 3;
                               bcf      v__status, v__c,v__access
                               rrcf     v_ustat,w,v__access
                               movwf    v___end_point_4,v__banked
                               bcf      v__status, v__c,v__access
                               rrcf     v___end_point_4,f,v__banked
                               bcf      v__status, v__c,v__access
                               rrcf     v___end_point_4,f,v__banked
;  320 	if USTAT_DIR then
                               btfss    v_ustat, 2,v__access ; ustat_dir
                               goto     l__l556
;  328 		pid = ( usb_bd0in_stat >> 2) & 0x0f
                               bcf      v__status, v__c,v__access
                               movlb    4
                               rrcf     v_usb_bd0in_stat,w,v__banked
                               movlb    3
                               movwf    v____temp_52,v__banked
                               bcf      v__status, v__c,v__access
                               rrcf     v____temp_52,f,v__banked
                               movlw    15
                               andwf    v____temp_52,w,v__banked
                               movwf    v_pid,v__banked
;  329 	else
                               goto     l__l555
l__l556
;  330 		pid = ( usb_bd0out_stat >> 2) & 0x0f
                               bcf      v__status, v__c,v__access
                               movlb    4
                               rrcf     v_usb_bd0out_stat,w,v__banked
                               movlb    3
                               movwf    v____temp_52,v__banked
                               bcf      v__status, v__c,v__access
                               rrcf     v____temp_52,f,v__banked
                               movlw    15
                               andwf    v____temp_52,w,v__banked
                               movwf    v_pid,v__banked
;  344 	end if
l__l555
;  356 	if ( end_point == 0 ) then
                               movf     v___end_point_4,w,v__banked
                               btfss    v__status, v__z,v__access
                               goto     l__l562
;  365 		case pid of
;  366 			USB_PID_SETUP:
                               movlw    13
                               subwf    v_pid,w,v__banked
                               btfss    v__status, v__z,v__access
                               goto     l__l564
;  367 			block
;  371 				for 8 using idx loop
                               clrf     v___idx_2,v__banked
l__l566
;  372 					usb_sdp[idx ] = src[idx ]
                               lfsr     0,v_src
                               movf     v___idx_2,w,v__banked
                               addwf    v__fsr0l,f,v__access
                               movf     v__ind,w,v__access
                               movlb    0
                               movwf    v__pic_temp,v__banked
                               lfsr     0,v_usb_sdp
                               movlb    3
                               movf     v___idx_2,w,v__banked
                               addwf    v__fsr0l,f,v__access
                               movlb    0
                               movf     v__pic_temp,w,v__banked
                               movwf    v__ind,v__access
;  373 				end loop
                               movlb    3
                               incf     v___idx_2,f,v__banked
                               movlw    8
                               subwf    v___idx_2,w,v__banked
                               btfss    v__status, v__z,v__access
                               goto     l__l566
;  384 			UCON_PKTDIS = low		
                               bcf      v_ucon, 4,v__access ; ucon_pktdis
;  386 			usb_prime_ep0_out()
                               call     l_usb_prime_ep0_out
;  403 				case ( usb_sdp_request_type  & 0b_0110_000 ) of
                               movlw    48
                               movlb    4
                               andwf    v_usb_sdp_request_type,w,v__banked
                               movlb    3
                               movwf    v____temp_52,v__banked
;  404 					(0b00 << USB_REQUEST_TYPE0_BIT ):
                               movf     v____temp_52,w,v__banked
                               btfss    v__status, v__z,v__access
                               goto     l__l571
;  405 					block
;  421 						_usb_handle_standard_request()
                               goto     l__usb_handle_standard_request
;  423 					end block
l__l571
;  424 					(0b01 << USB_REQUEST_TYPE0_BIT ):
                               movlw    32
                               subwf    v____temp_52,w,v__banked
                               btfss    v__status, v__z,v__access
                               goto     l__l575
;  425 					block					
;  432 							usb_handle_class_request_callback()
                               goto     l_usb_handle_class_request_callback
;  433 						end if	
;  434 					end block
l__l575
;  435 					(0b10 << USB_REQUEST_TYPE0_BIT ):
                               movlw    64
                               subwf    v____temp_52,w,v__banked
                               btfss    v__status, v__z,v__access
                               goto     l__l561
;  445 					end block
;  458 					end block
l__l574
;  460 			end block
                               return   
l__l564
;  463 			USB_PID_IN:
                               movlw    9
                               subwf    v_pid,w,v__banked
                               btfss    v__status, v__z,v__access
                               goto     l__l588
;  464 			block
;  471 				case usb_control_mode of
;  472 					USB_CM_CTRL_READ_DATA_STAGE:
                               movlw    3
                               movlb    0
                               subwf    v_usb_control_mode,w,v__banked
                               btfss    v__status, v__z,v__access
                               goto     l__l591
;  473 					block
;  475 						usb_send_data_chunk()				
                               goto     l_usb_send_data_chunk
;  476 					end block
l__l591
;  478 					USB_CM_CTRL_WRITE_SENDING_STATUS:
                               movlw    6
                               subwf    v_usb_control_mode,w,v__banked
                               btfss    v__status, v__z,v__access
                               goto     l__l594
;  479 					block
;  481 						usb_control_mode = USB_CM_IDLE
                               clrf     v_usb_control_mode,v__banked
;  482 						if (usb_status == USB_STATUS_SET_ADDRESS) then
                               movlw    1
                               subwf    v_usb_status,w,v__banked
                               btfss    v__status, v__z,v__access
                               goto     l__l561
;  491 							usb_state = USB_STATE_ADDRESS
                               movlw    2
                               movwf    v_usb_state,v__banked
;  492 							uaddr = usb_address
                               movf     v_usb_address,w,v__banked
                               movwf    v_uaddr,v__access
;  495 							usb_status = USB_STATUS_IDLE
                               clrf     v_usb_status,v__banked
;  496 						end if
;  502 					end block
                               return   
l__l594
;  504 					USB_CM_CTRL_READ_AWAITING_STATUS:
                               movlw    5
                               subwf    v_usb_control_mode,w,v__banked
                               btfsc    v__status, v__z,v__access
;  510 					end block
                               return   
l__l600
;  512 					USB_CM_CTRL_READ_DATA_STAGE_CLASS:
                               movlw    4
                               subwf    v_usb_control_mode,w,v__banked
                               btfss    v__status, v__z,v__access
                               goto     l__l603
;  513 					block
;  520 							usb_handle_class_ctrl_read_callback();
;  522 					end block
l__l603
;  534 			end block
                               return   
l__l588
;  537 			USB_PID_ACK:
                               movlw    2
                               subwf    v_pid,w,v__banked
                               btfss    v__status, v__z,v__access
                               goto     l__l611
;  538 			block
;  545 				case usb_control_mode of
;  546 					USB_CM_CTRL_READ_DATA_STAGE: 
                               movlw    3
                               movlb    0
                               subwf    v_usb_control_mode,w,v__banked
                               btfss    v__status, v__z,v__access
                               goto     l__l614
;  547 					block
;  552 						usb_send_data_chunk()
                               goto     l_usb_send_data_chunk
;  553 					end block
l__l614
;  555 					USB_CM_CTRL_READ_DATA_STAGE_CLASS: 
                               movlw    4
                               subwf    v_usb_control_mode,w,v__banked
                               btfsc    v__status, v__z,v__access
;  556 					block
;  558 							usb_handle_class_ctrl_read_callback()
;  559 						end if	
                               return   
;  560 					end block
l__l618
;  561 					USB_CM_CTRL_WRITE_SENDING_STATUS: 
                               movlw    6
                               subwf    v_usb_control_mode,w,v__banked
                               btfss    v__status, v__z,v__access
                               goto     l__l561
;  562 					block
;  567 						usb_control_mode = USB_CM_IDLE
                               clrf     v_usb_control_mode,v__banked
;  568 					end block
;  569 				end case
l__l617
;  570 			end block
                               return   
l__l611
;  573 			USB_PID_OUT:
                               movlw    1
                               subwf    v_pid,w,v__banked
                               btfss    v__status, v__z,v__access
                               goto     l__l561
;  574 			block
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
